QUT-Motorsport/QUTMS_Radio/RelatedImages/0150180559MolexFlatFlex.PNG

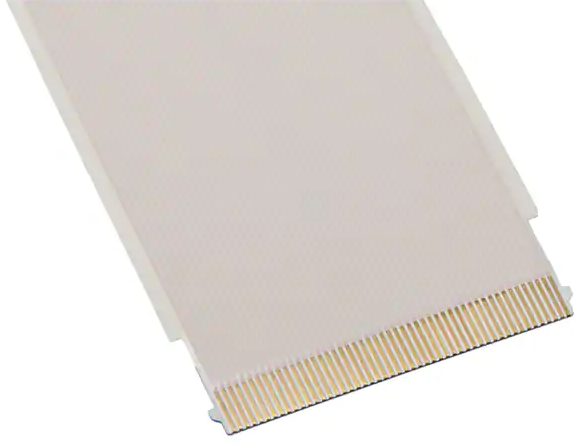
RelatedImages/0150180559MolexFlatFlex.PNG
