QUT-Motorsport/QUTMS_Radio/RelatedImages/bargraphDisplay.jpg

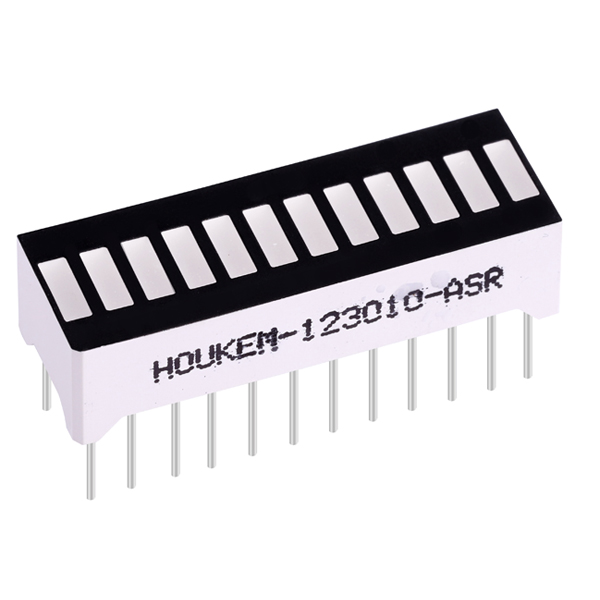
RelatedImages/bargraphDisplay.jpg
