QUT-Motorsport/QUTMS_Radio/RelatedImages/BMI-S-206-C.PNG

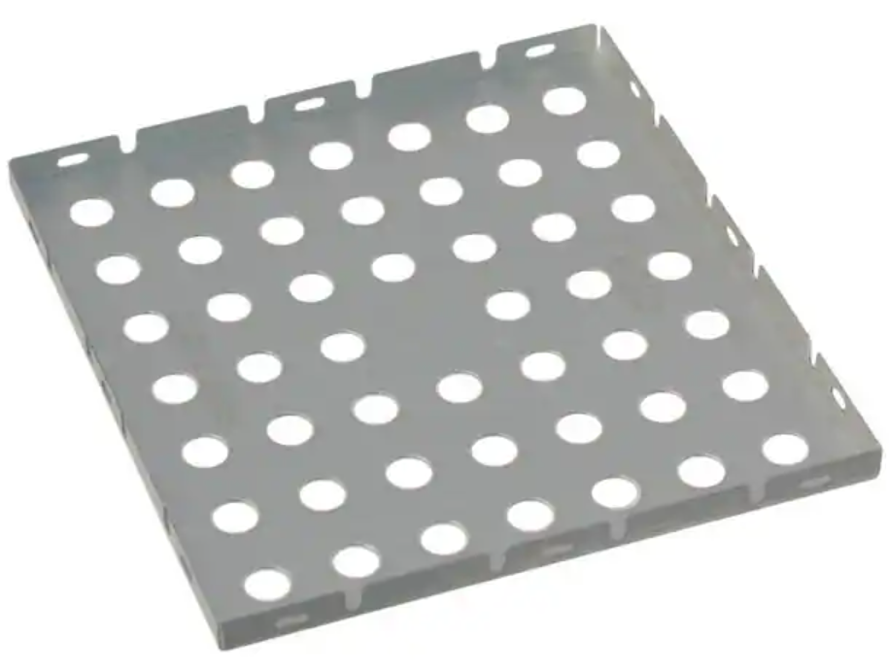
RelatedImages/BMI-S-206-C.PNG
