QUT-Motorsport/QUTMS_Radio/RelatedImages/BMI-S-206-F.PNG

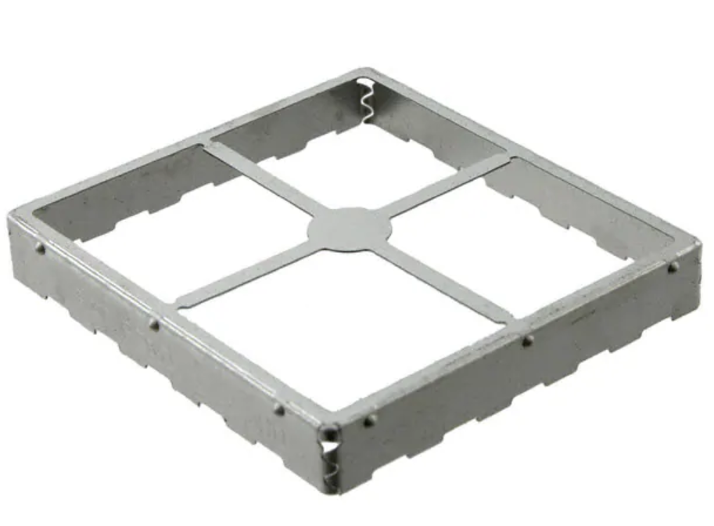
RelatedImages/BMI-S-206-F.PNG
