QUT-Motorsport/QUTMS_Radio/RelatedImages/cr2032battery.jpg

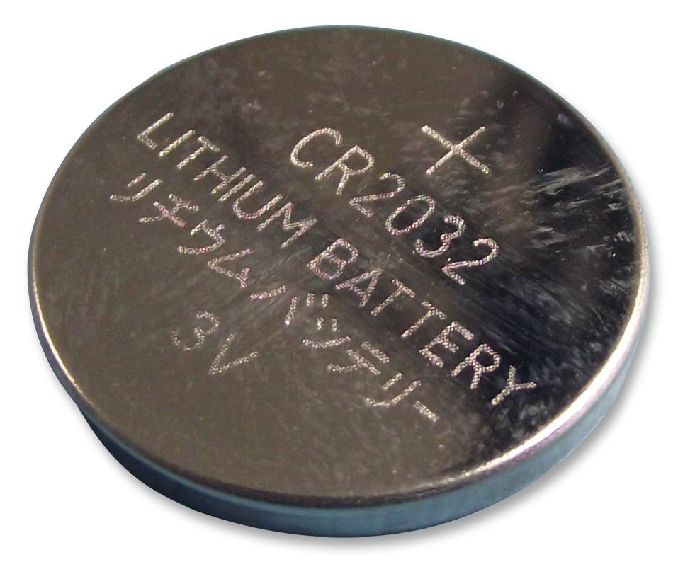
RelatedImages/cr2032battery.jpg
