QUT-Motorsport/QUTMS_Radio/RelatedImages/daughterBoardExample.png

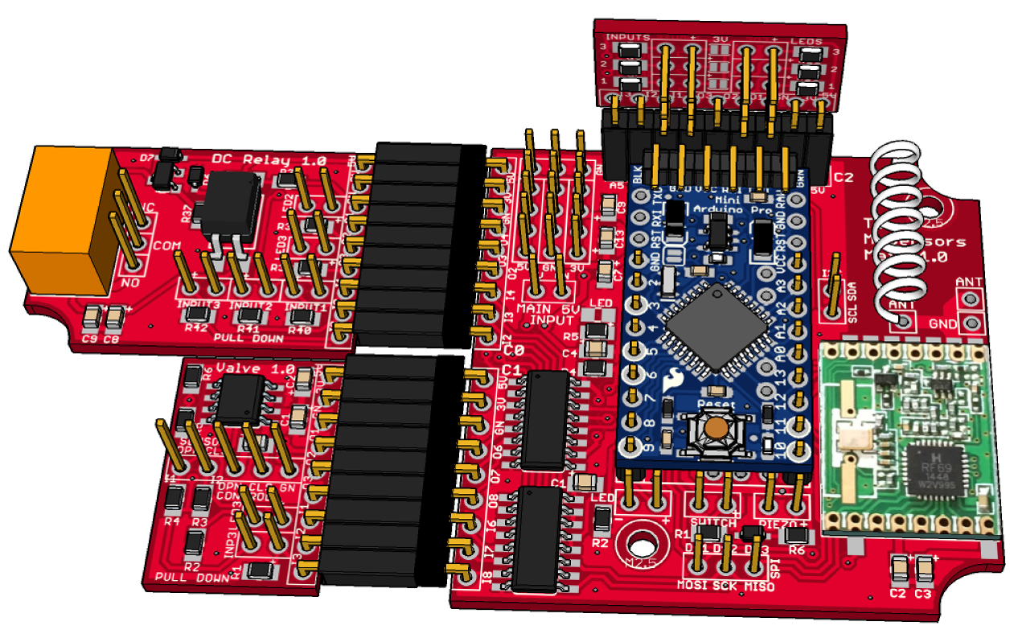
RelatedImages/daughterBoardExample.png
