QUT-Motorsport/QUTMS_Radio/RelatedImages/DBP868UA.PNG

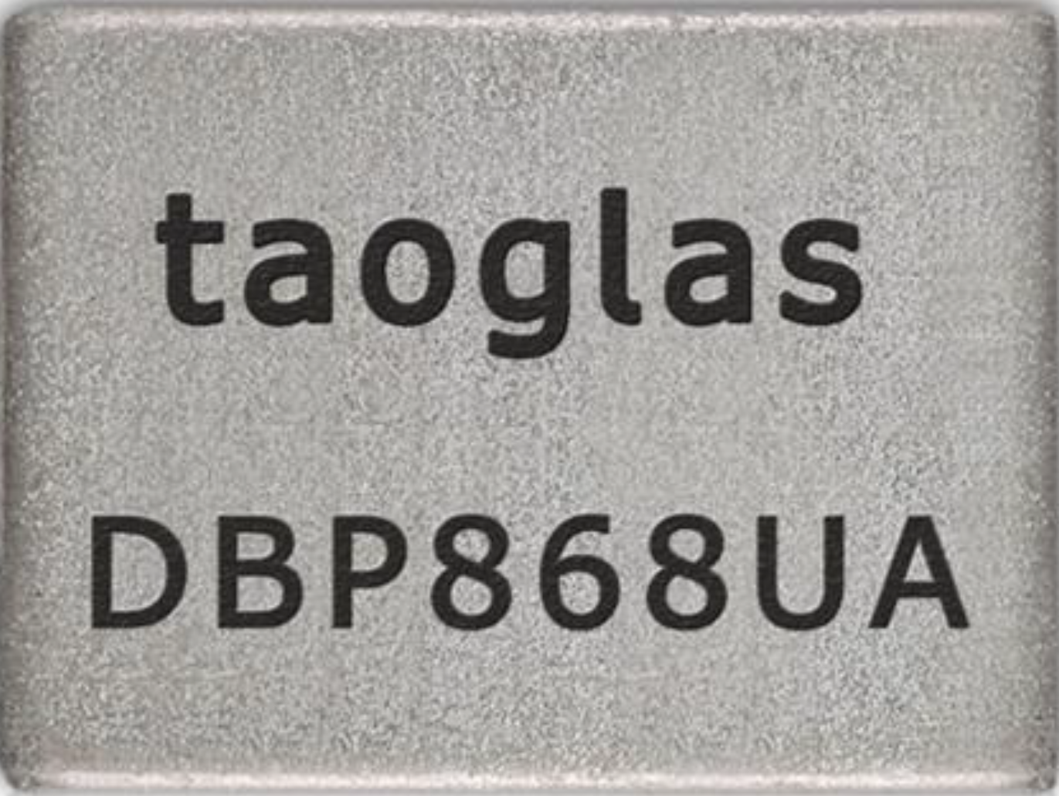
RelatedImages/DBP868UA.PNG
