QUT-Motorsport/QUTMS_Radio/RelatedImages/DBP915VA.PNG

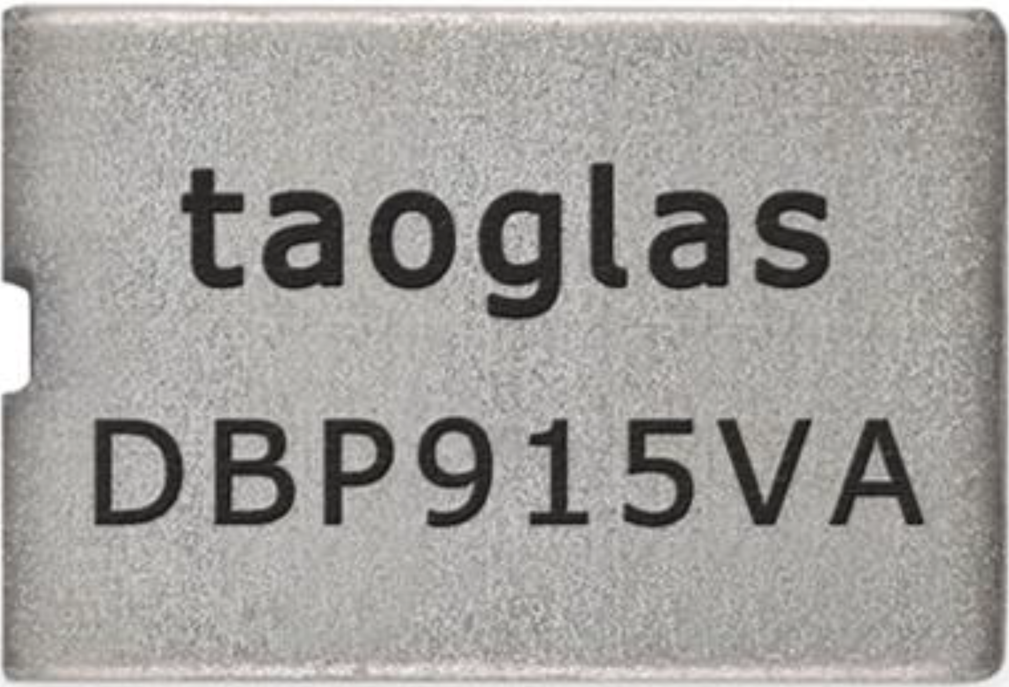
RelatedImages/DBP915VA.PNG
