QUT-Motorsport/QUTMS_Radio/RelatedImages/dcBarrelJack_PJ-102AH.PNG

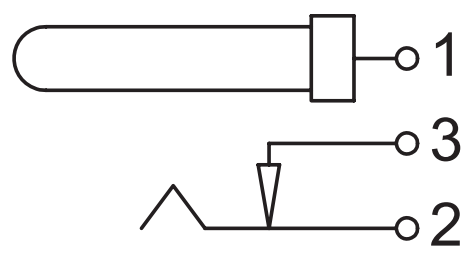
RelatedImages/dcBarrelJack_PJ-102AH.PNG
