QUT-Motorsport/QUTMS_Radio/RelatedImages/driverlessTrack.PNG

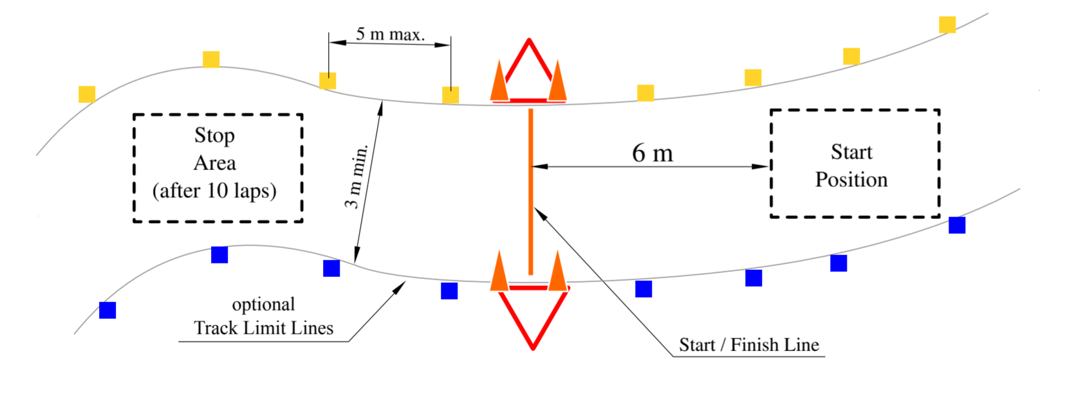
RelatedImages/driverlessTrack.PNG
