QUT-Motorsport/QUTMS_Radio/RelatedImages/dualMX120G.png

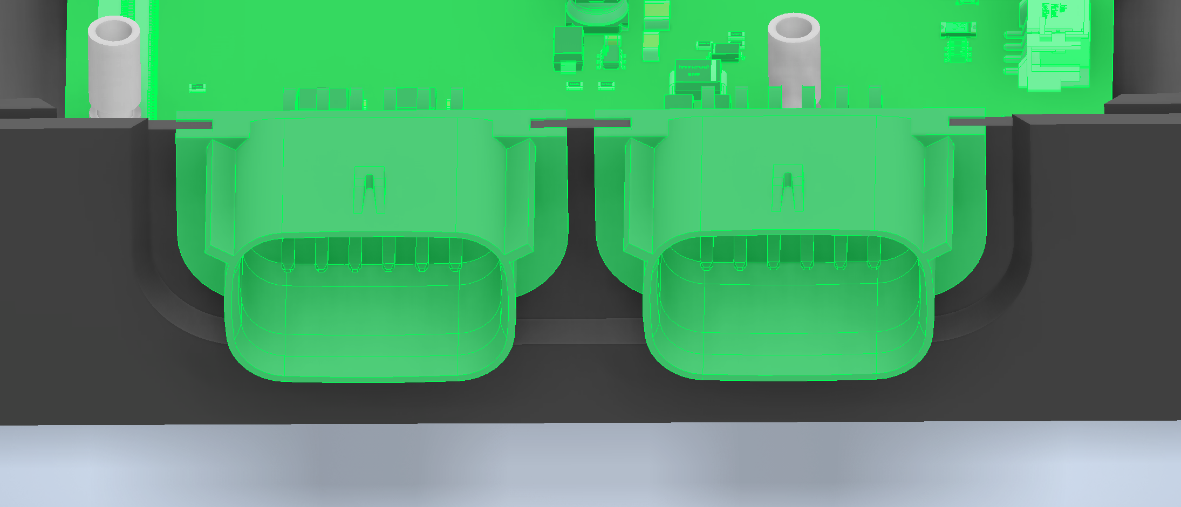
RelatedImages/dualMX120G.png
