QUT-Motorsport/QUTMS_Radio/RelatedImages/EOSRegions.png

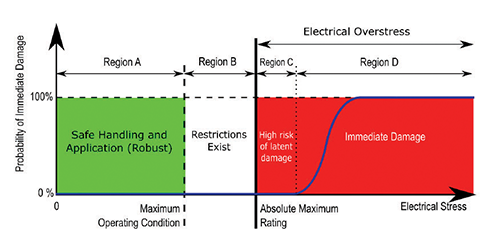
RelatedImages/EOSRegions.png
