QUT-Motorsport/QUTMS_Radio/RelatedImages/EOSRootCauses.png

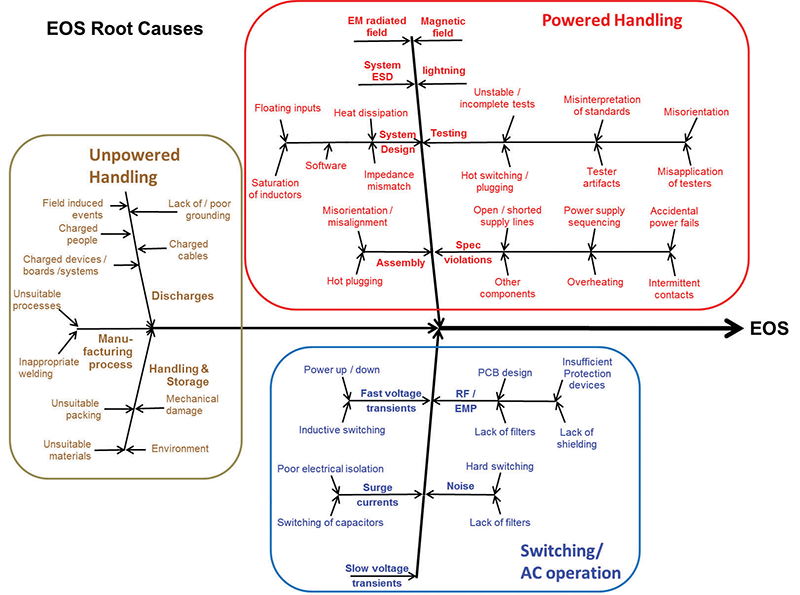
RelatedImages/EOSRootCauses.png
