QUT-Motorsport/QUTMS_Radio/RelatedImages/gnssComparisonGraph-01.png

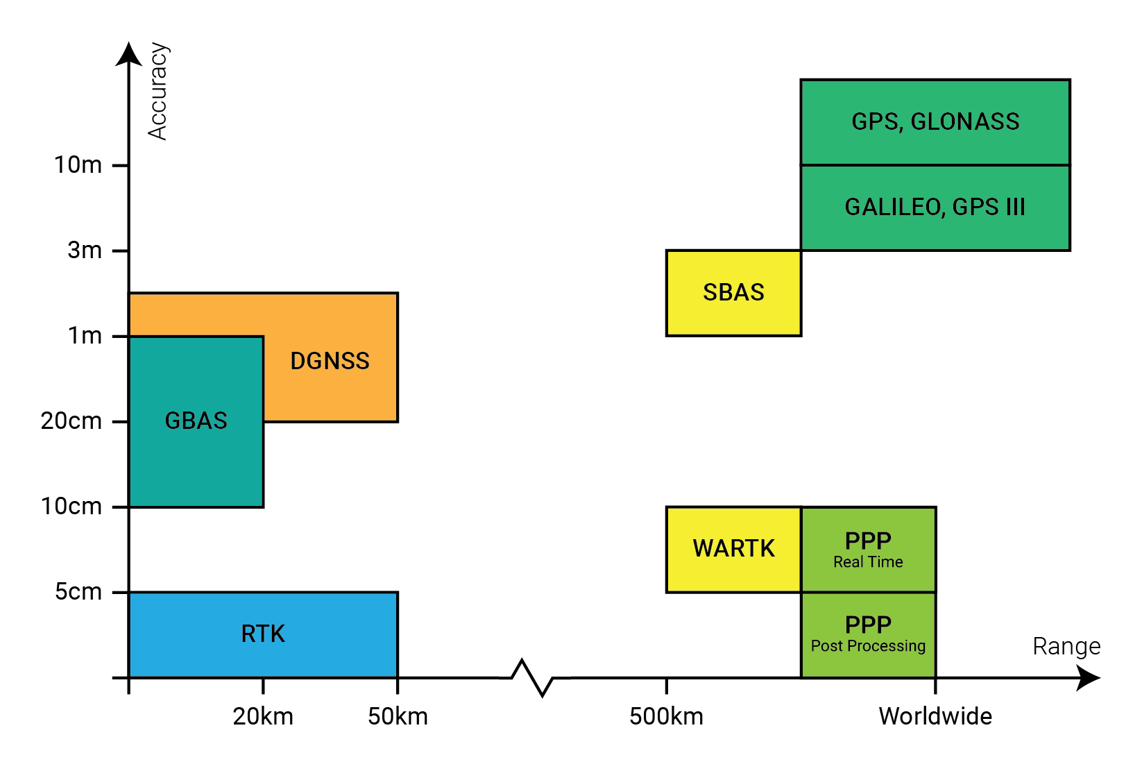
RelatedImages/gnssComparisonGraph-01.png
