QUT-Motorsport/QUTMS_Radio/RelatedImages/gpsSelection.PNG

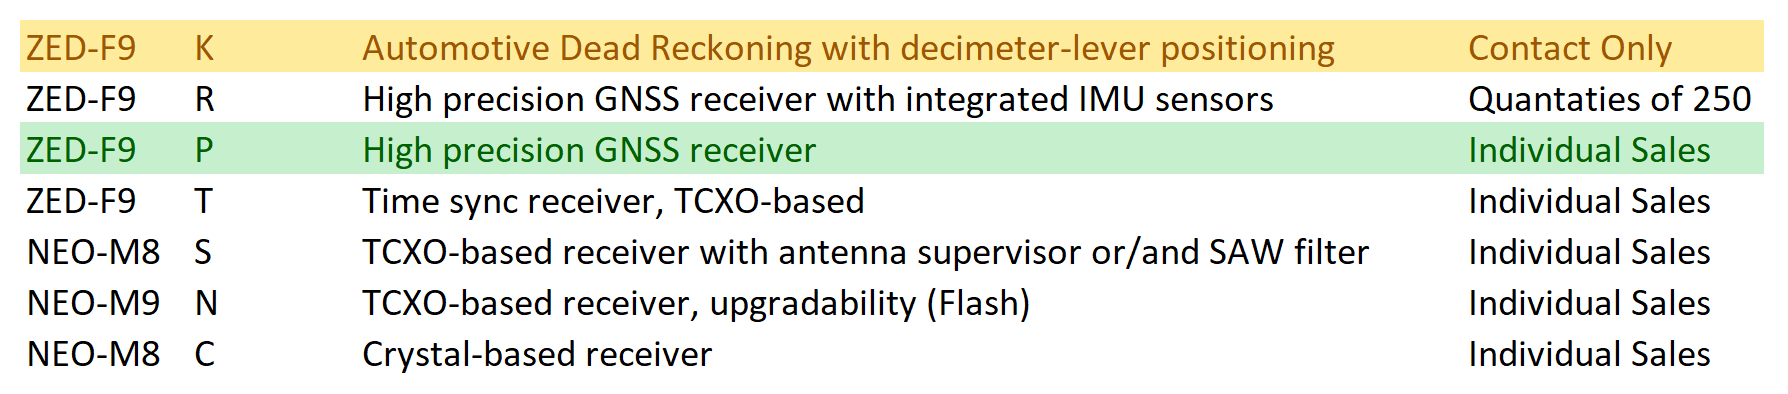
RelatedImages/gpsSelection.PNG
