QUT-Motorsport/QUTMS_Radio/RelatedImages/interimCaseTopDown.jpg

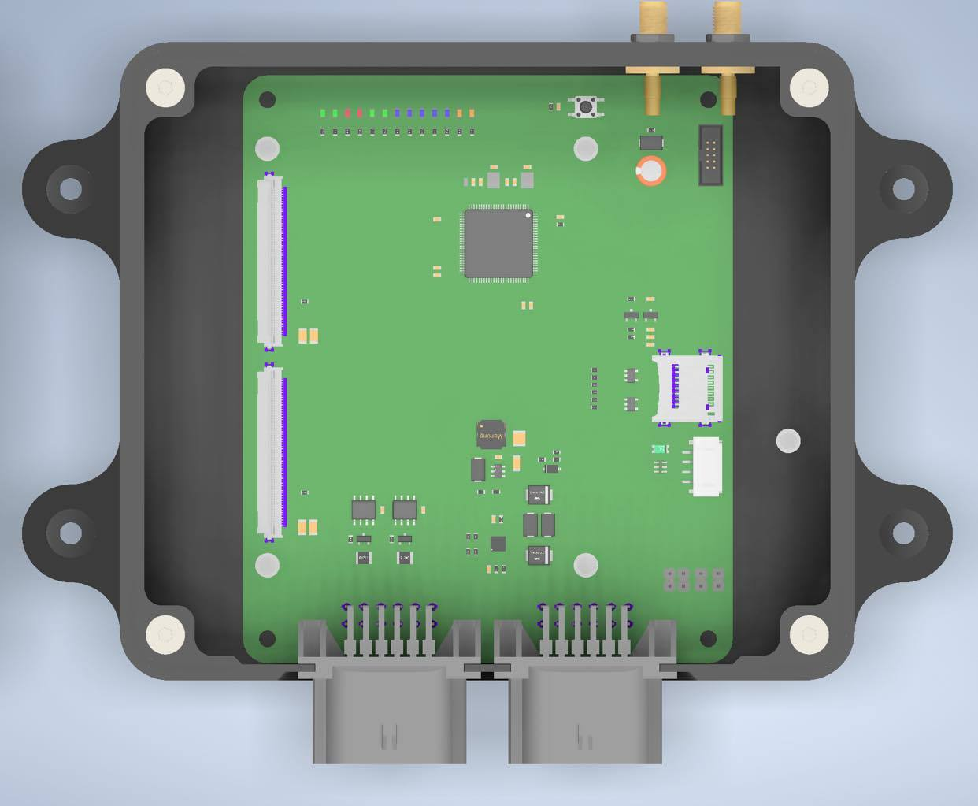
RelatedImages/interimCaseTopDown.jpg
