QUT-Motorsport/QUTMS_Radio/RelatedImages/m2mSelection.PNG

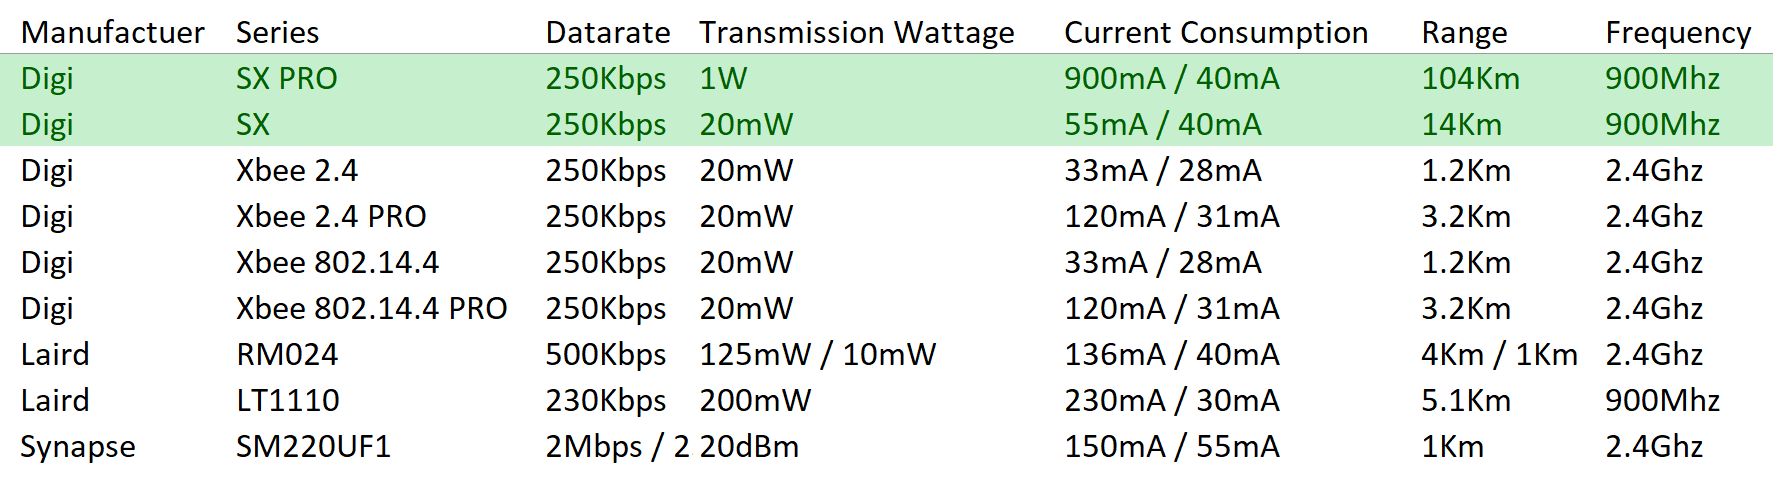
RelatedImages/m2mSelection.PNG
