QUT-Motorsport/QUTMS_Radio/RelatedImages/MX120G_FrontOn.PNG

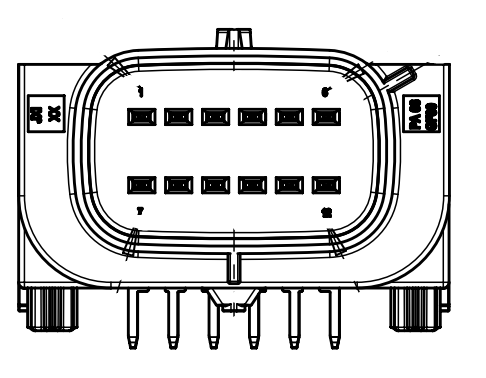
RelatedImages/MX120G_FrontOn.PNG
