QUT-Motorsport/QUTMS_Radio/RelatedImages/pcbWay4LayerStackUp.PNG

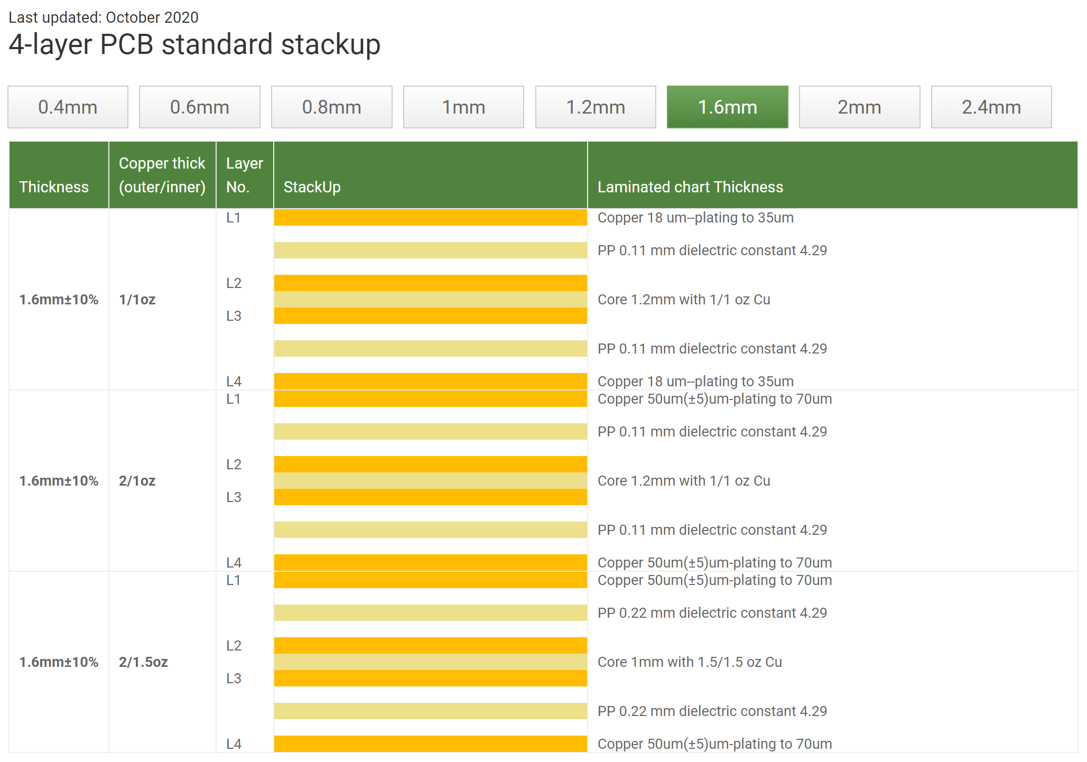
RelatedImages/pcbWay4LayerStackUp.PNG
