QUT-Motorsport/QUTMS_Radio/RelatedImages/RadioPodDistances-01.png

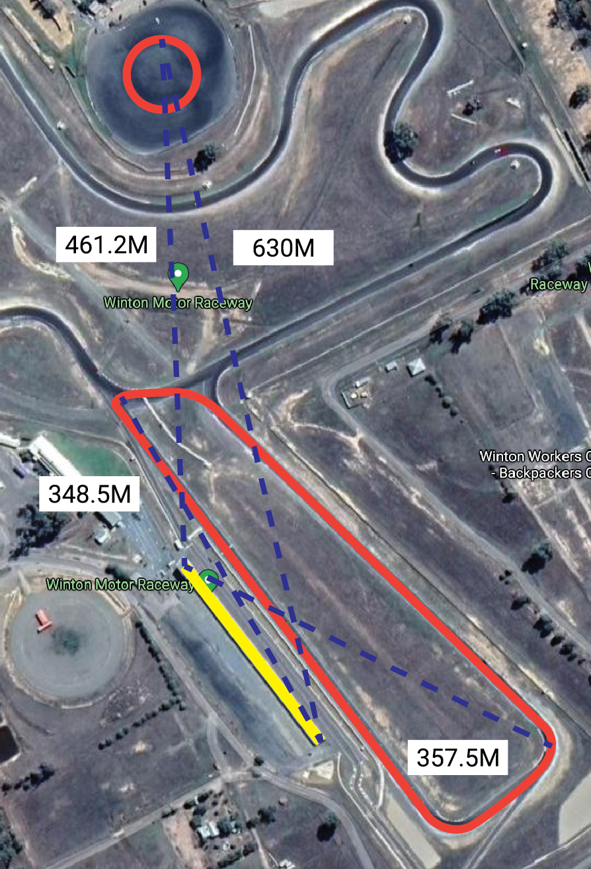
RelatedImages/RadioPodDistances-01.png
