QUT-Motorsport/QUTMS_Radio/RelatedImages/RadioPodDistances-02.png

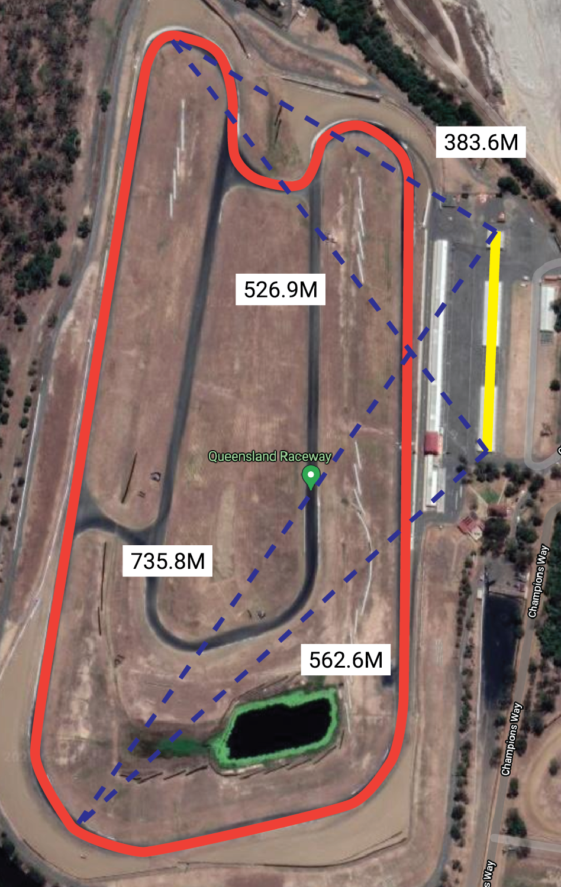
RelatedImages/RadioPodDistances-02.png
