QUT-Motorsport/QUTMS_Radio/RelatedImages/rtkImplimenation.PNG

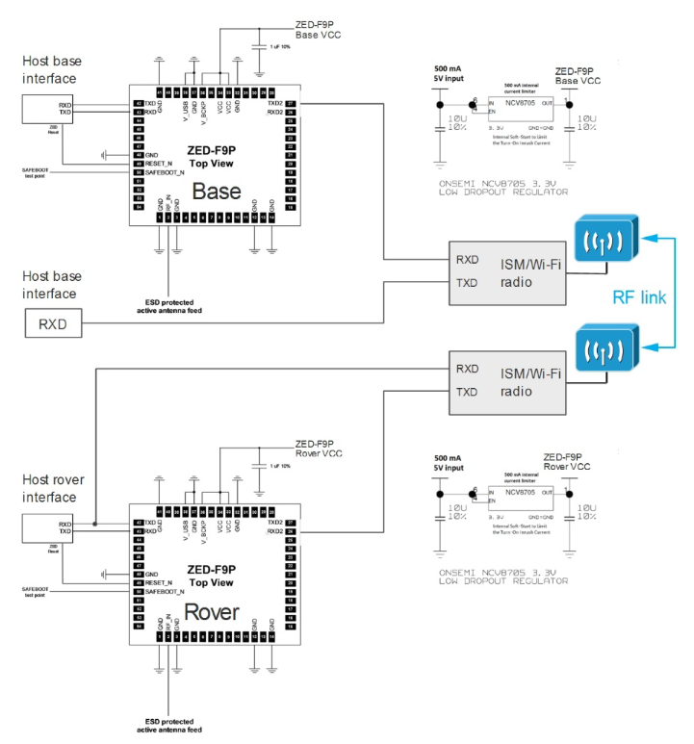
RelatedImages/rtkImplimenation.PNG
