QUT-Motorsport/QUTMS_Radio/RelatedImages/rulesFSGDriverlessRadioComms.PNG

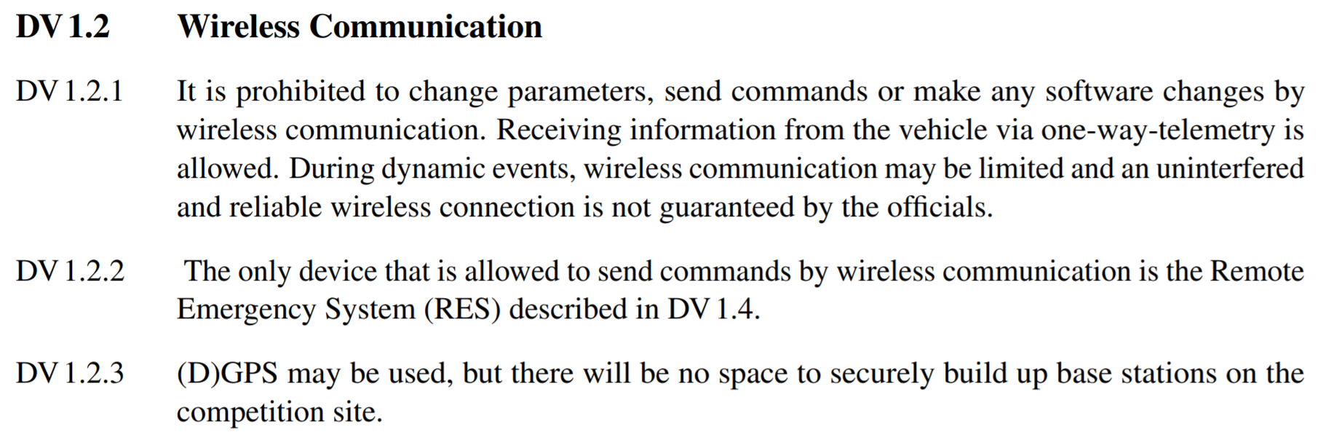
RelatedImages/rulesFSGDriverlessRadioComms.PNG
