QUT-Motorsport/QUTMS_Radio/RelatedImages/rulesFSGDriverlessSuppliedRadio.PNG

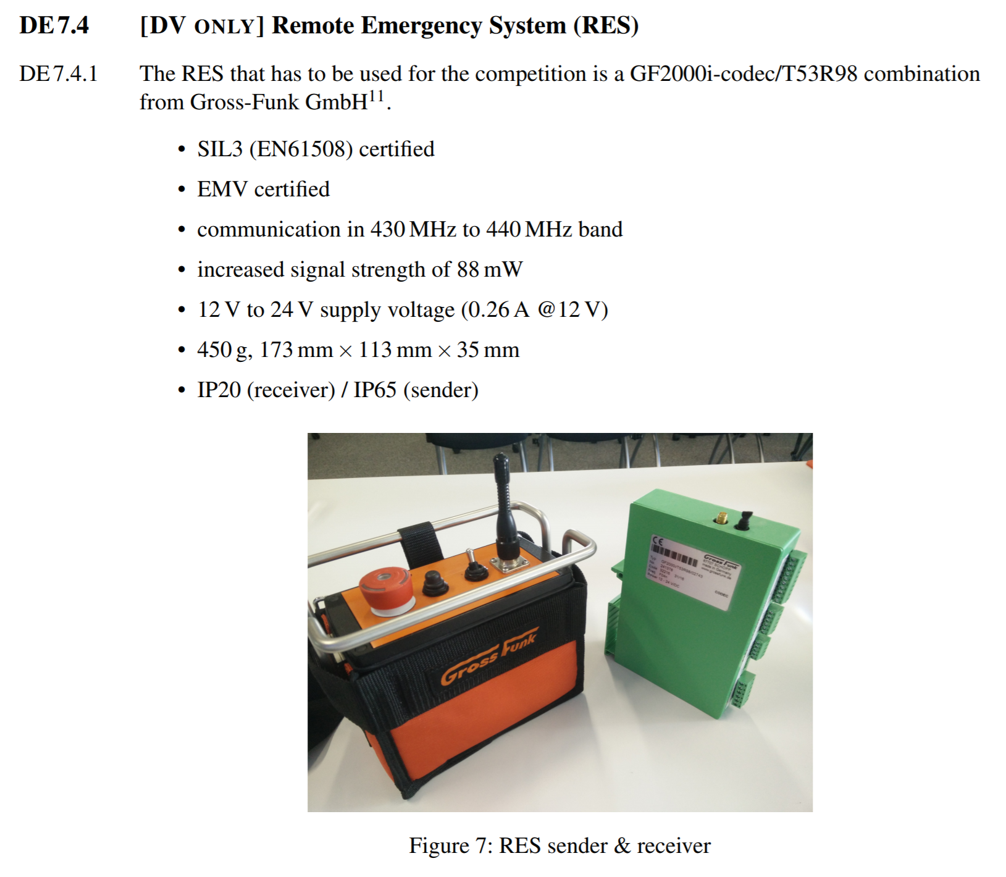
RelatedImages/rulesFSGDriverlessSuppliedRadio.PNG
