QUT-Motorsport/QUTMS_Radio/RelatedImages/serial_spi_i2c_yellow_1.5_inch_arduino_raspberry_pi_oled_display_128x64.jpg

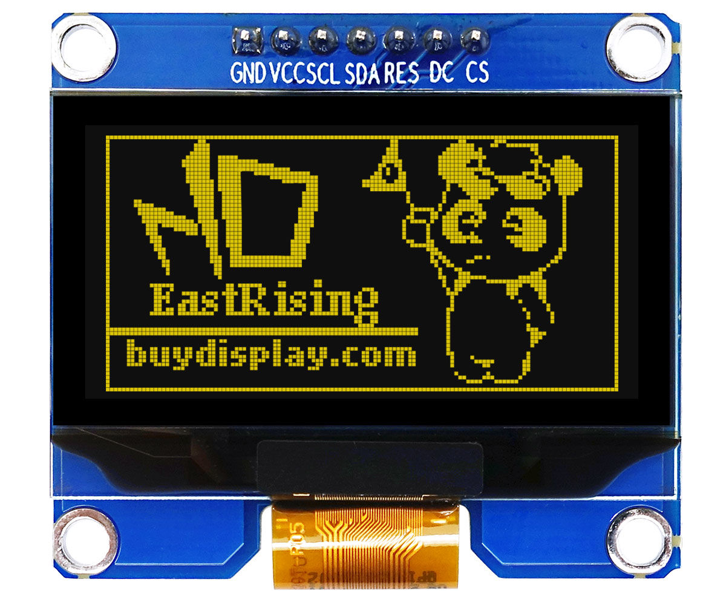
RelatedImages/serial_spi_i2c_yellow_1.5_inch_arduino_raspberry_pi_oled_display_128x64.jpg
