QUT-Motorsport/QUTMS_Radio/RelatedImages/sevenSegDisplay.png

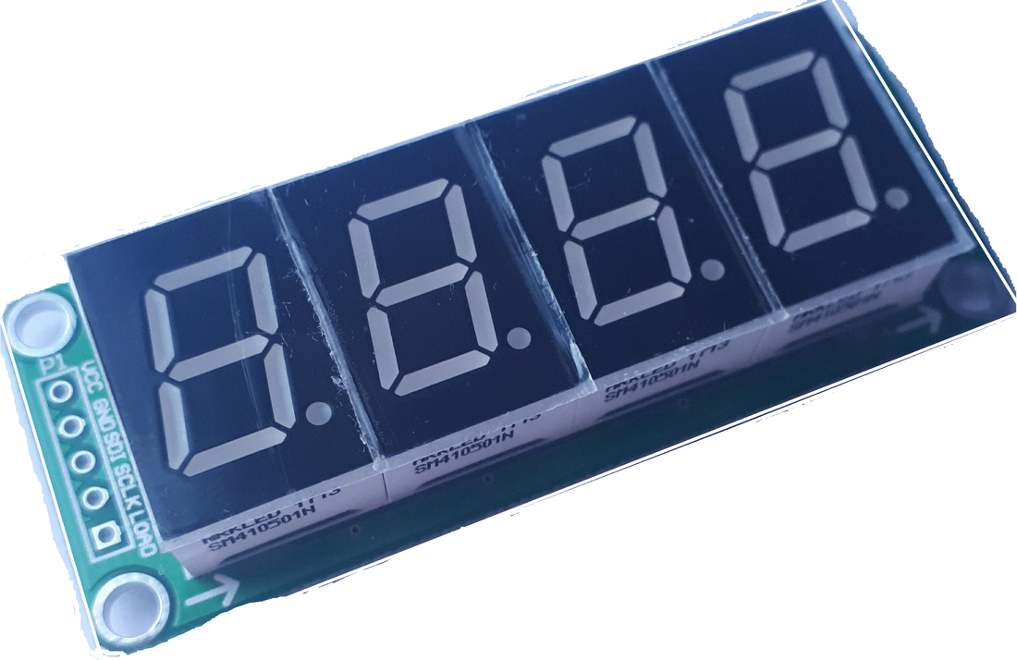
RelatedImages/sevenSegDisplay.png
