QUT-Motorsport/QUTMS_Radio/RelatedImages/supercapGenericImage.PNG

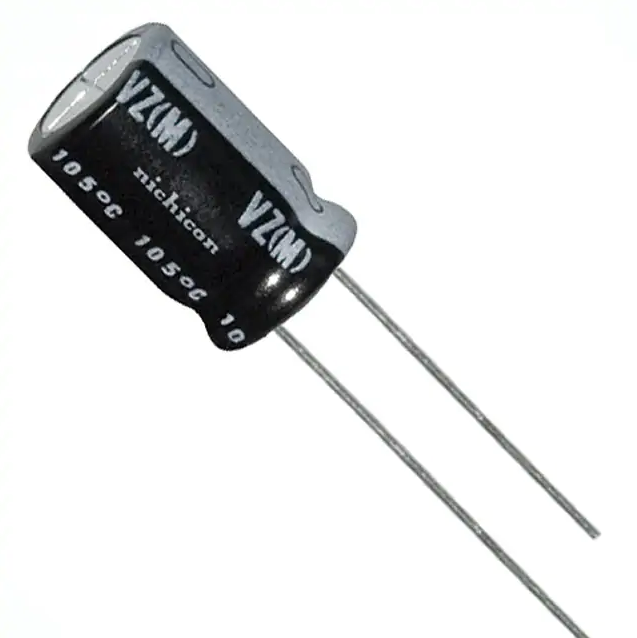
RelatedImages/supercapGenericImage.PNG
