QUT-Motorsport/QUTMS_Radio/RelatedImages/taoglasAntenna_AA200151111.PNG

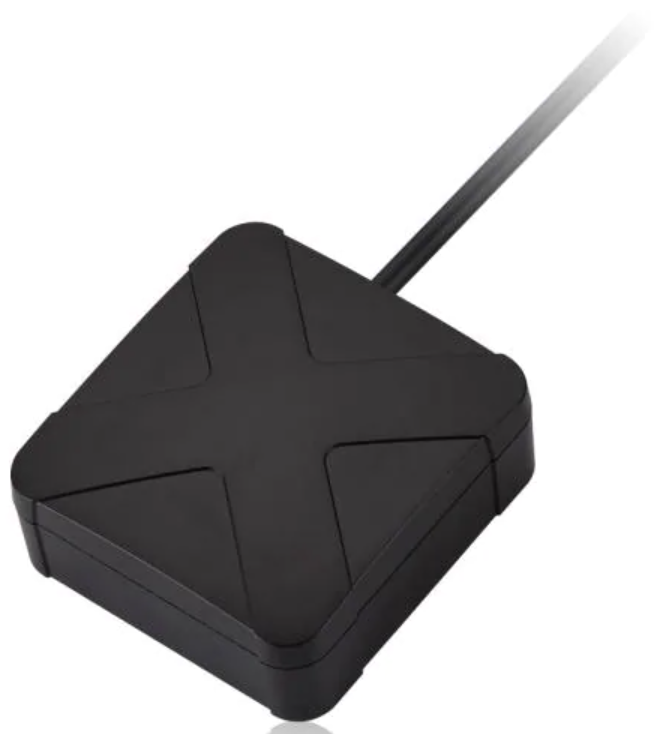
RelatedImages/taoglasAntenna_AA200151111.PNG
