QUT-Motorsport/QUTMS_Radio/RelatedImages/taoglasAntennaISM.PNG

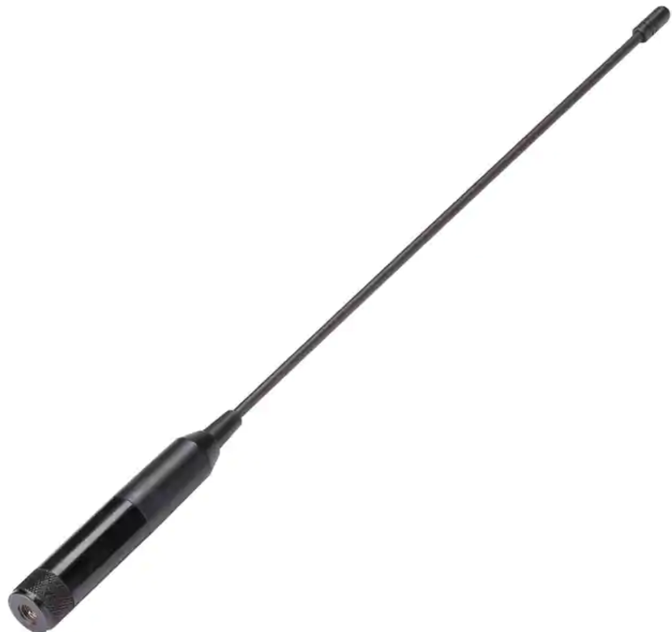
RelatedImages/taoglasAntennaISM.PNG
