QUT-Motorsport/QUTMS_Radio/RelatedImages/u-blox ZED-F9P decal.png

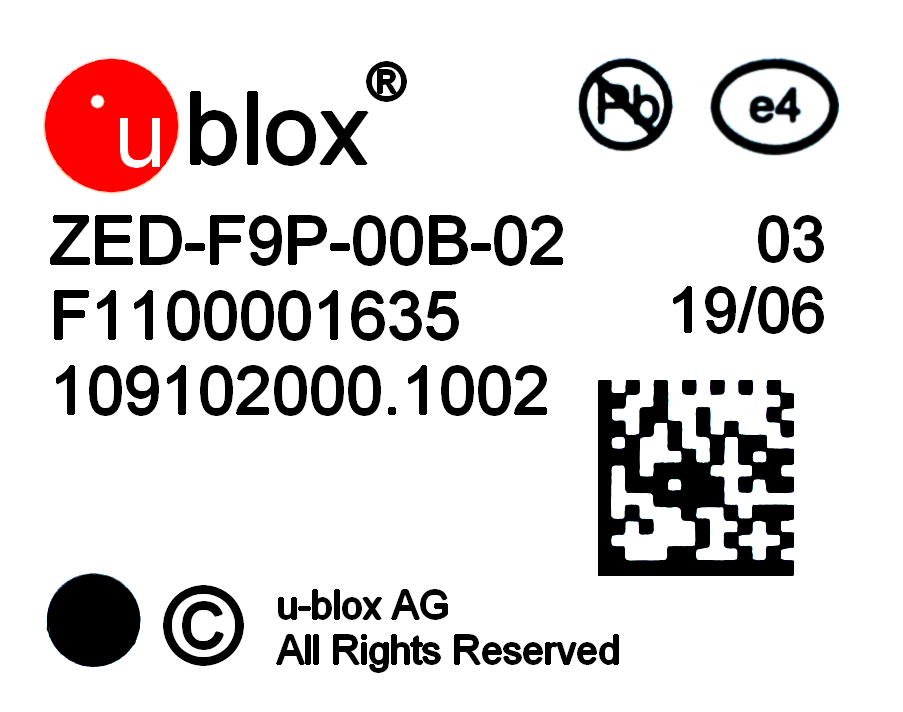
RelatedImages/u-blox ZED-F9P decal.png
