QUT-Motorsport/QUTMS_Radio/RelatedImages/ublox_FullColor_CMYK_pos_0.jpg

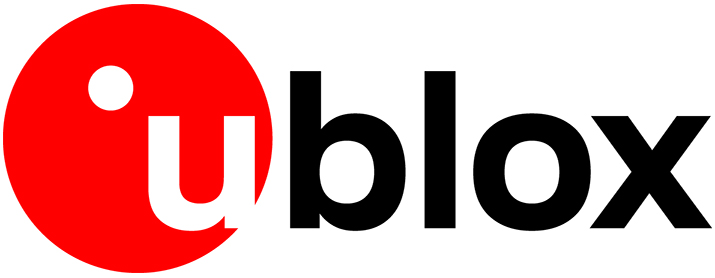
RelatedImages/ublox_FullColor_CMYK_pos_0.jpg
