QUT-Motorsport/QUTMS_Radio/3DModels/OLEDDisplay1-3inch.stp

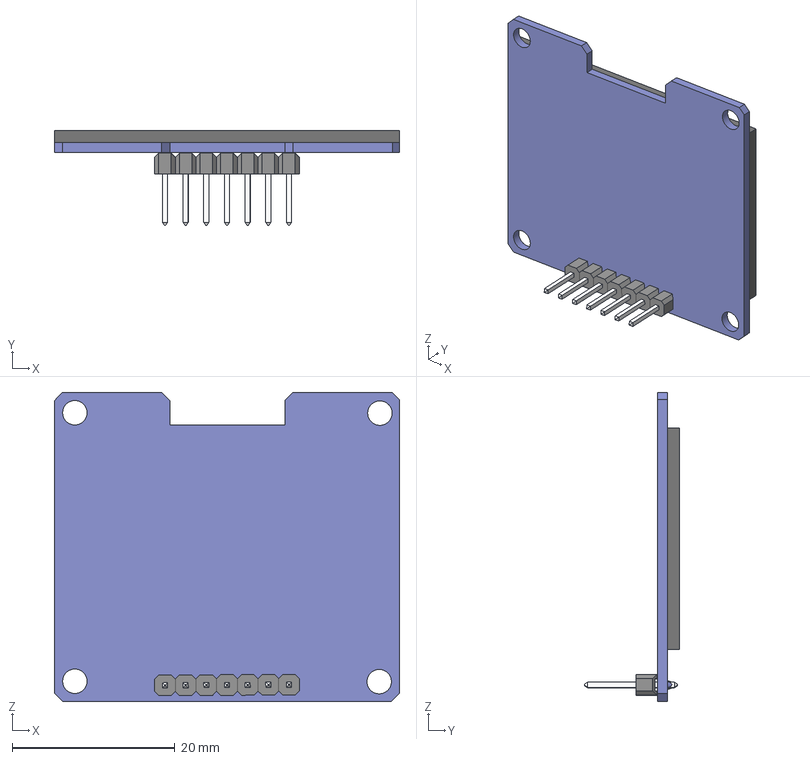
[picture p52: CAD file, 2021-02-18]
3DModels/OLEDDisplay1-3inch.stp
42.4 x 11.7 x 38.0 mm
