QUT-Motorsport/QUTMS_Radio/3DModels/1812_RES.stp

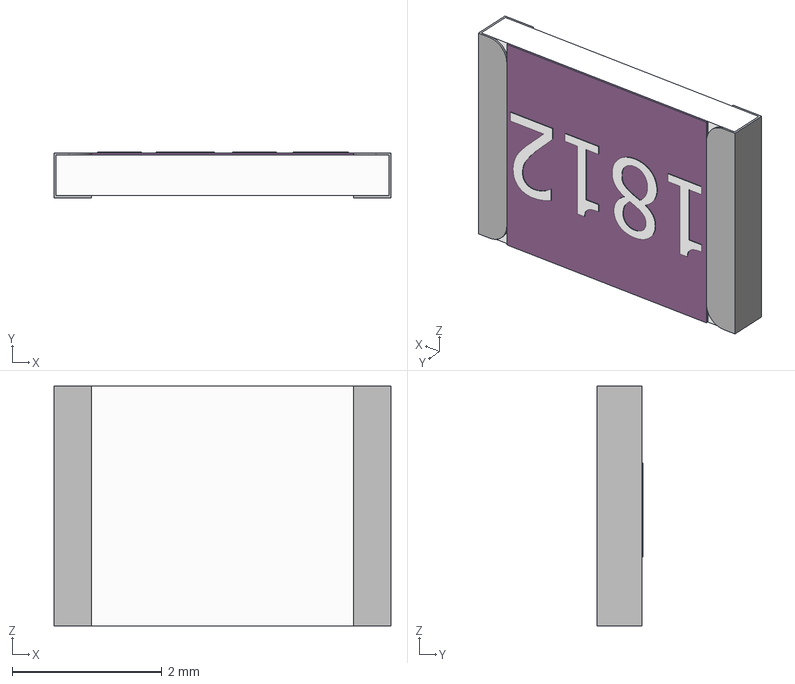
[picture p53: CAD file, 2021-02-15]
3DModels/1812_RES.stp
4.50 x 0.61 x 3.20 mm
Capsule
Encapsulation x 2
TopCover
