QUT-Motorsport/QUTMS_Radio/3DModels/TSSOP-14 0.65p 4.4mm.step

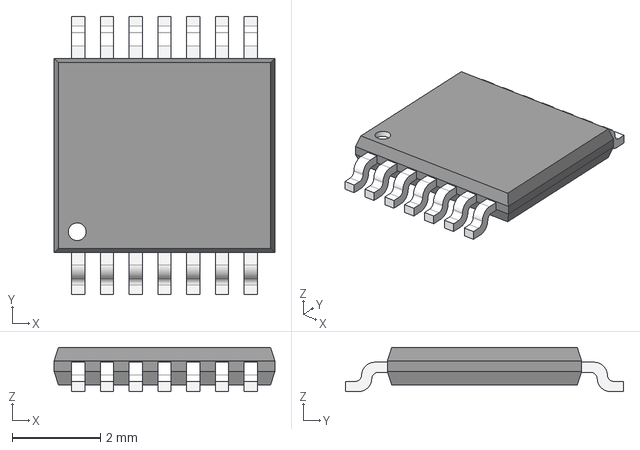
[picture p54: CAD file, 2021-02-15]
3DModels/TSSOP-14 0.65p 4.4mm.step
5.00 x 6.30 x 1.00 mm
