QUT-Motorsport/QUTMS_Radio/3DModels/pqfpfp144_p0-5_l20_w20.stp

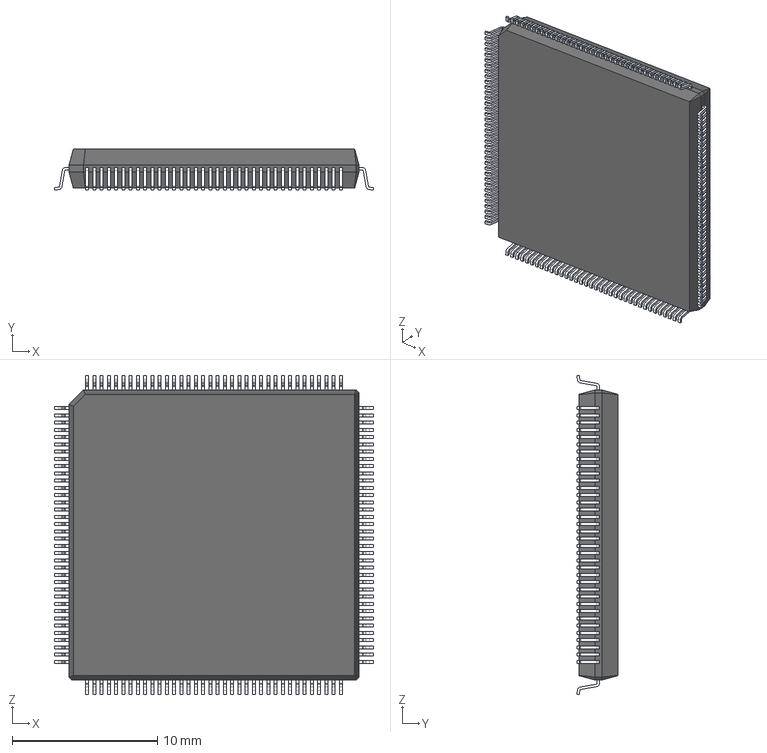
[picture p55: CAD file, 2021-02-11]
3DModels/pqfpfp144_p0-5_l20_w20.stp
22.0 x 2.83 x 22.0 mm
