QUT-Motorsport/QUTMS_Radio/3DModels/hexagonal_spacer_MF_M3_H10_HEX5_FTD6_MTL8.step

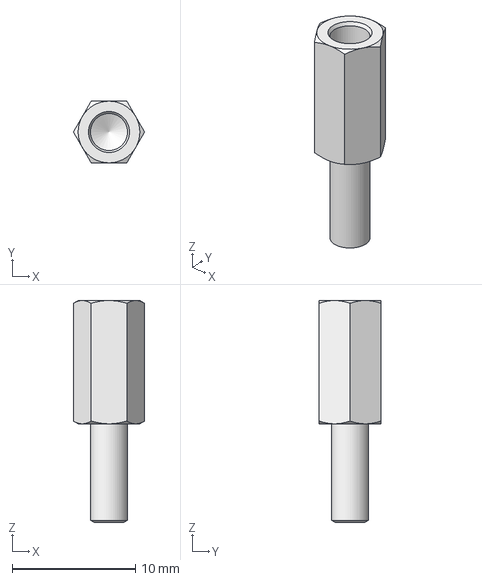
[picture p57: CAD file, 2021-02-09]
3DModels/hexagonal_spacer_MF_M3_H10_HEX5_FTD6_MTL8.step
5.78 x 5.01 x 18.0 mm
