QUT-Motorsport/QUTMS_Radio/3DModels/hexagonal_spacer_MF_M3_H08_HEX5_FTD4_MTL8.step

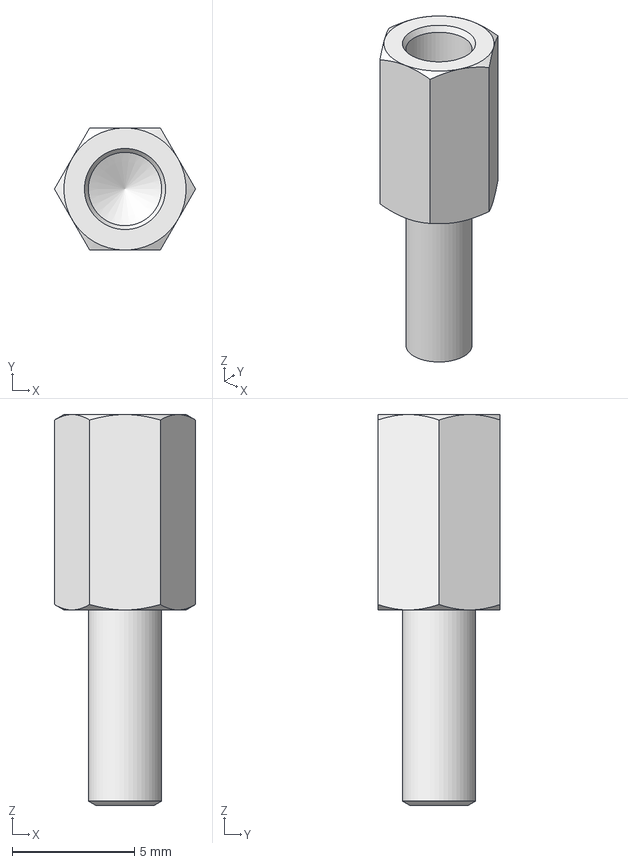
[picture p58: CAD file, 2021-02-09]
3DModels/hexagonal_spacer_MF_M3_H08_HEX5_FTD4_MTL8.step
5.78 x 5.01 x 16.0 mm
