QUT-Motorsport/QUTMS_Radio/3DModels/hexagonal_spacer_MF_M3_H12_HEX5_FTD8_MTL8.step

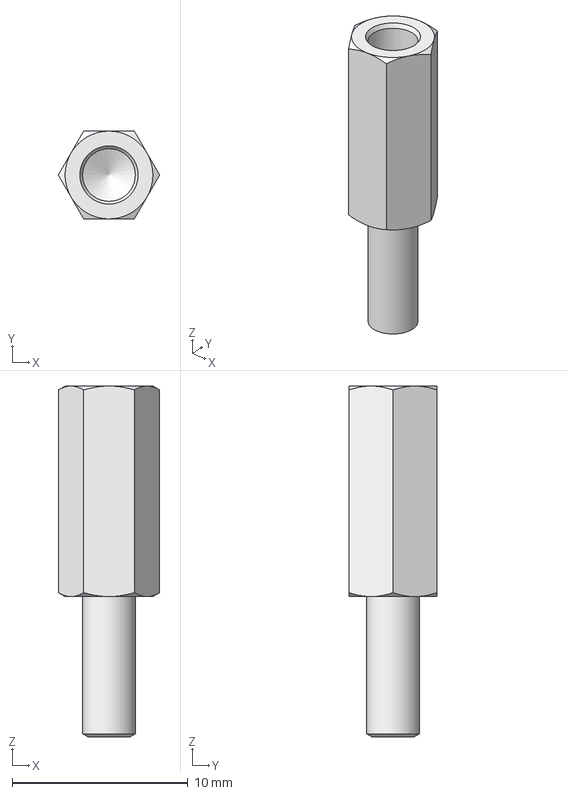
[picture p59: CAD file, 2021-02-09]
3DModels/hexagonal_spacer_MF_M3_H12_HEX5_FTD8_MTL8.step
5.78 x 5.01 x 20.0 mm
