QUT-Motorsport/QUTMS_Radio/3DModels/TSW-104-08-T-D-RA.stp

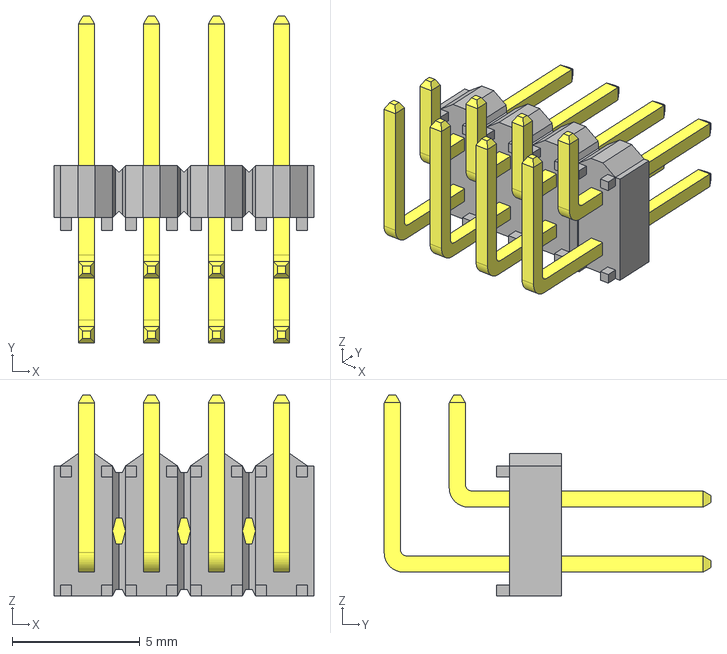
[picture p60: CAD file, 2021-02-08]
3DModels/TSW-104-08-T-D-RA.stp
10.2 x 12.8 x 7.85 mm
_TSW-104-08-T-D-RA_body
_T-1S6-08-TSW-1-08-4-RA-D
