QUT-Motorsport/QUTMS_Radio/3DModels/20-Pin Shrouded Header (IDC) Straight.stp

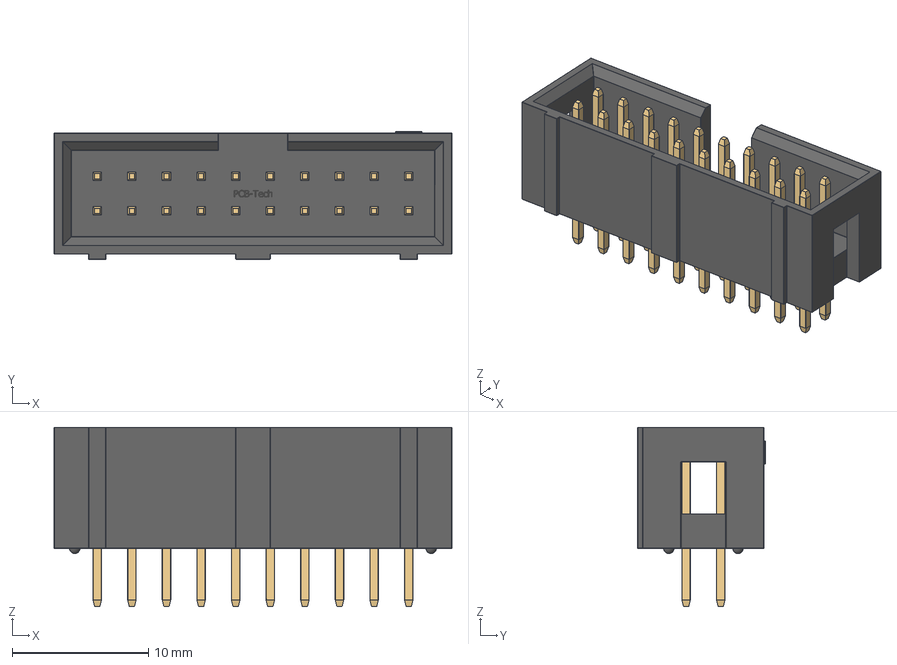
[picture p61: CAD file, 2021-02-08]
3DModels/20-Pin Shrouded Header (IDC) Straight.stp
29.2 x 9.37 x 13.2 mm
Straight Contact x 20
20-Pin Shrouded Header Body
