QUT-Motorsport/QUTMS_Radio/3DModels/LQFP100_14X14X1.6_P0.5_ST.step

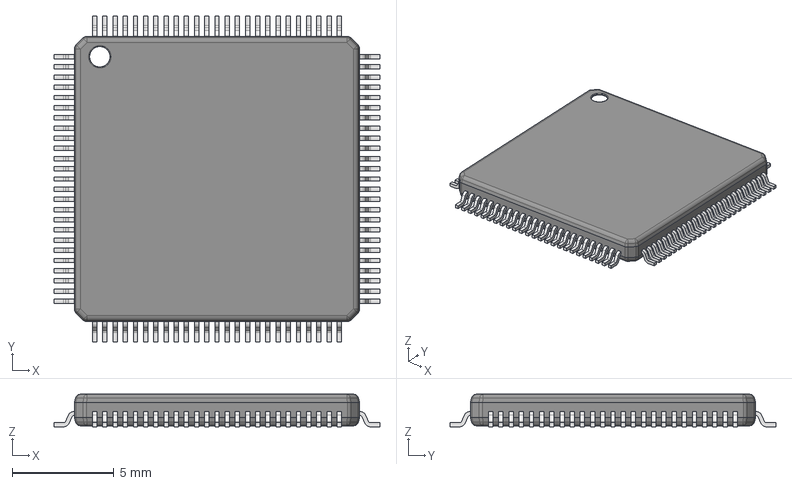
[picture p62: CAD file, 2021-02-05]
3DModels/LQFP100_14X14X1.6_P0.5_ST.step
16.0 x 16.0 x 1.60 mm
