QUT-Motorsport/QUTMS_Radio/3DModels/Aluminum_electrolytic_capacitor_radial_D6.3_H9_PinD0.5_Pitch2.5_nominal_orange.step

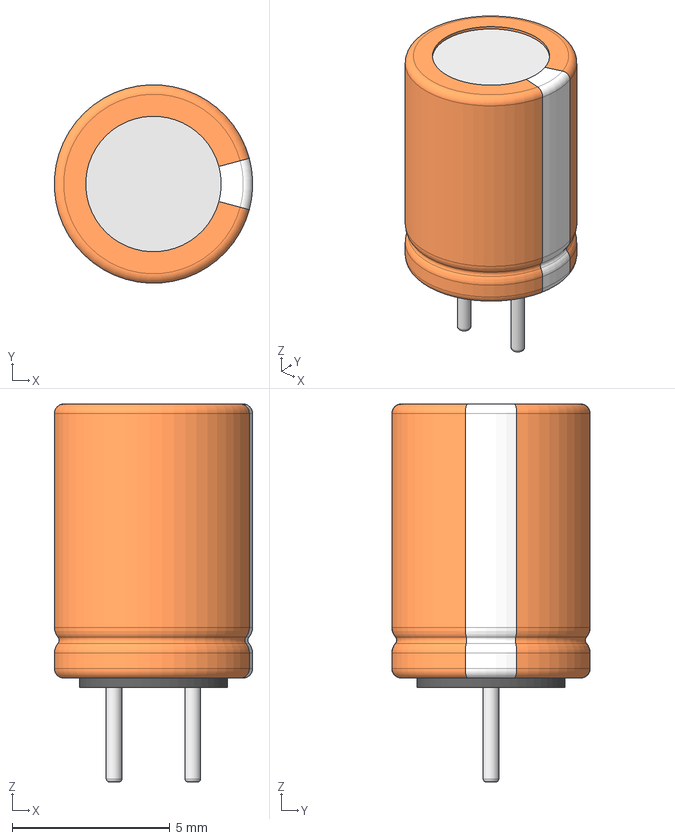
[picture p63: CAD file, 2021-02-04]
3DModels/Aluminum_electrolytic_capacitor_radial_D6.3_H9_PinD0.5_Pitch2.5_nominal_orange.step
6.29 x 6.30 x 12.0 mm
