QUT-Motorsport/QUTMS_Radio/3DModels/JST - PH - SMD (R) - 4Pin - 2.00mm.stp

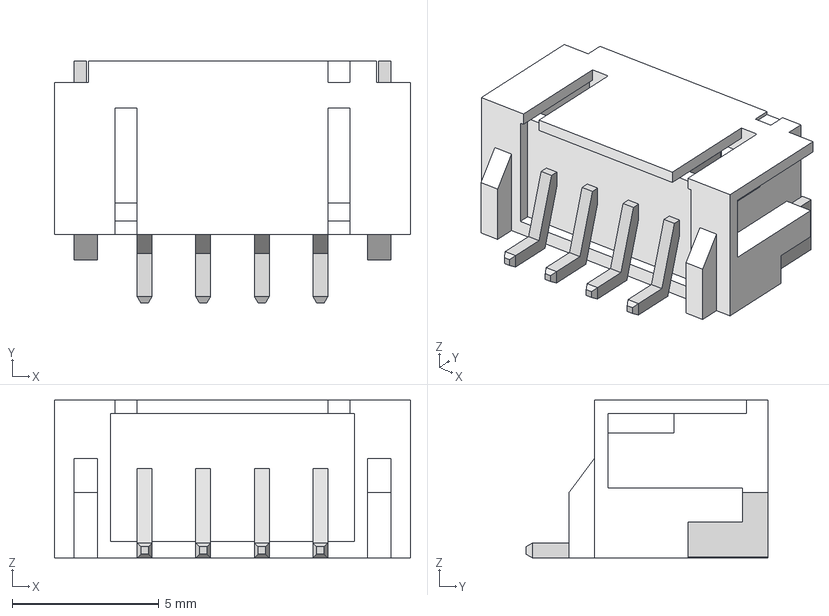
[picture p64: CAD file, 2021-02-04]
3DModels/JST - PH - SMD (R) - 4Pin - 2.00mm.stp
12.1 x 8.26 x 5.38 mm
