QUT-Motorsport/QUTMS_Radio/3DModels/JST - PH - Thru (V) - 4Pin - 2.00mm.stp

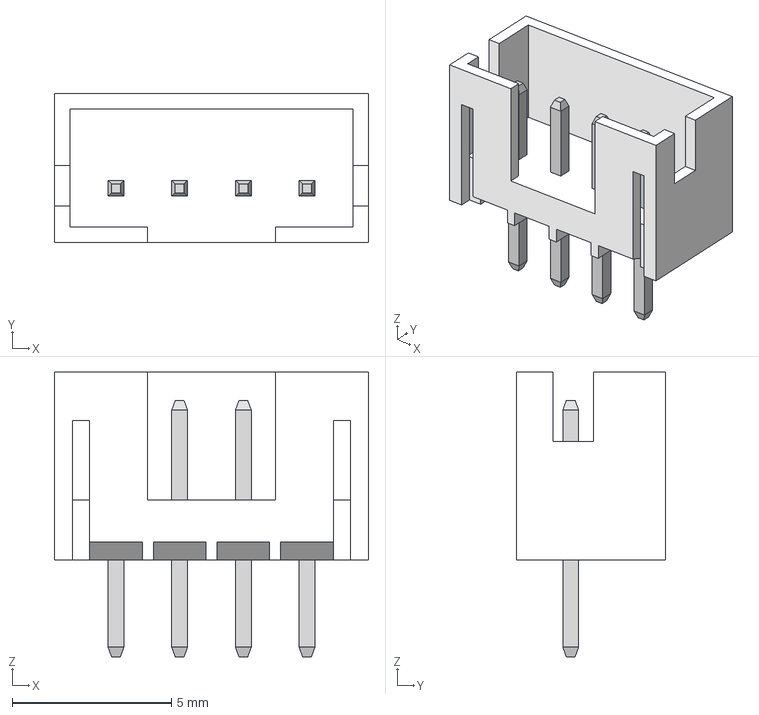
[picture p65: CAD file, 2021-02-04]
3DModels/JST - PH - Thru (V) - 4Pin - 2.00mm.stp
9.86 x 4.67 x 8.94 mm
