QUT-Motorsport/QUTMS_Radio/3DModels/SOT-223-6.step

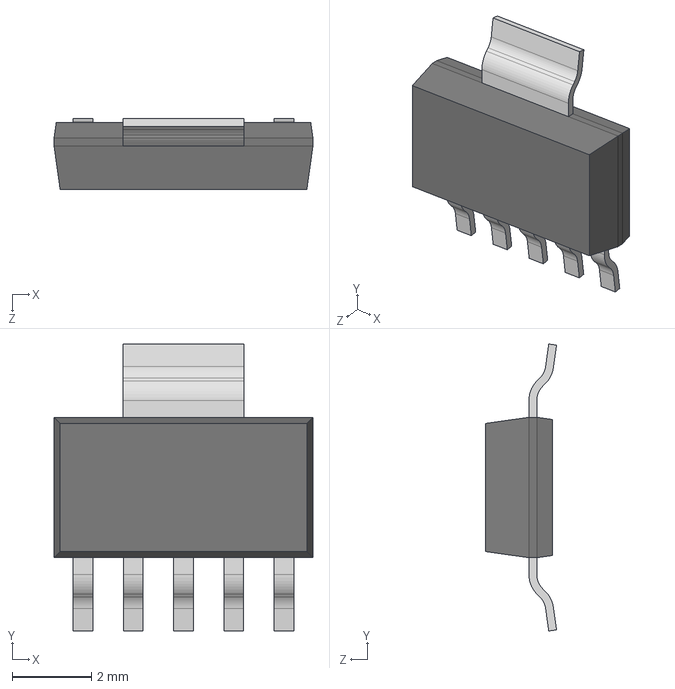
[picture p66: CAD file, 2021-02-04]
3DModels/SOT-223-6.step
6.55 x 7.26 x 1.80 mm
