QUT-Motorsport/QUTMS_Radio/3DModels/keystone-PN2898.STEP

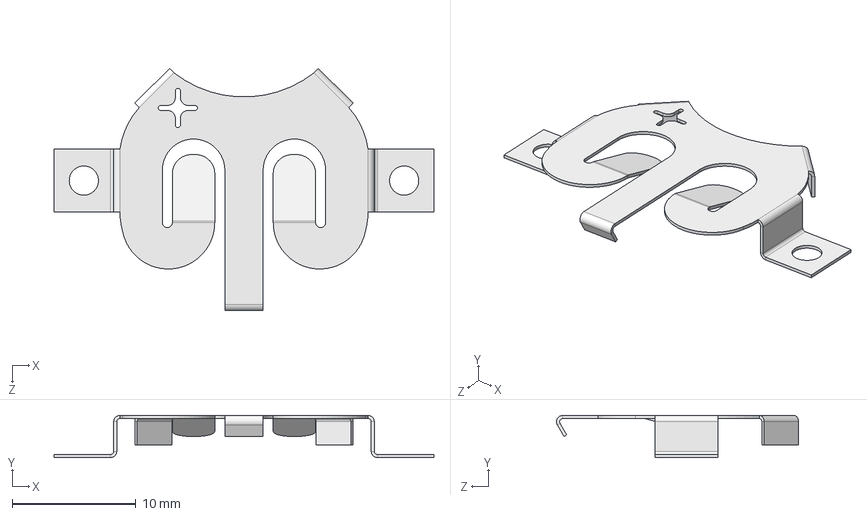
[picture p67: CAD file, 2021-02-03]
3DModels/keystone-PN2898.STEP
30.7 x 3.40 x 19.6 mm
