QUT-Motorsport/QUTMS_Radio/3DModels/U.FL-R-SMT(10)--3DModel-STEP-56544.STEP

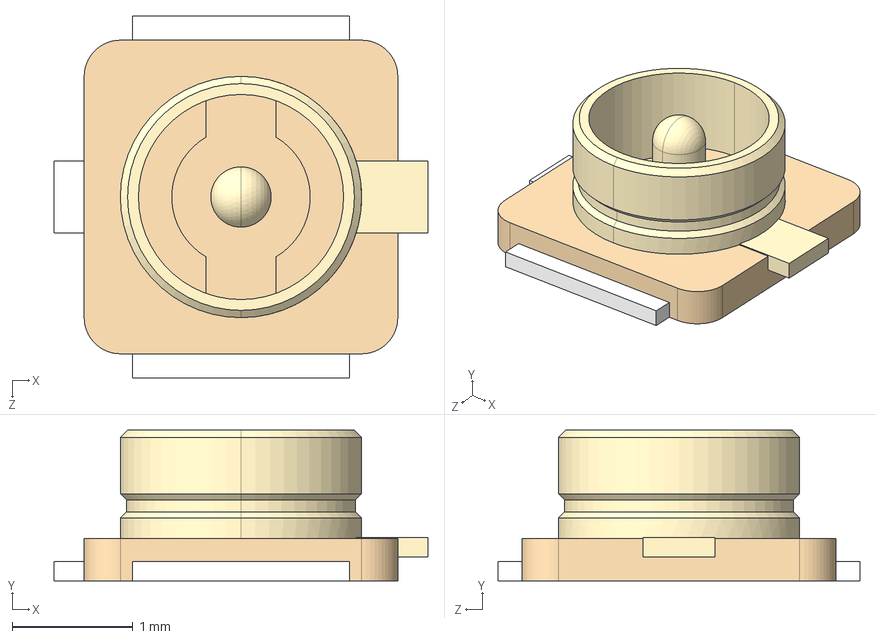
[picture p68: CAD file, 2021-02-03]
3DModels/U.FL-R-SMT(10)--3DModel-STEP-56544.STEP
3.10 x 1.25 x 3.00 mm
