QUT-Motorsport/QUTMS_Radio/3DModels/NFE31PT101C1E9L.STEP

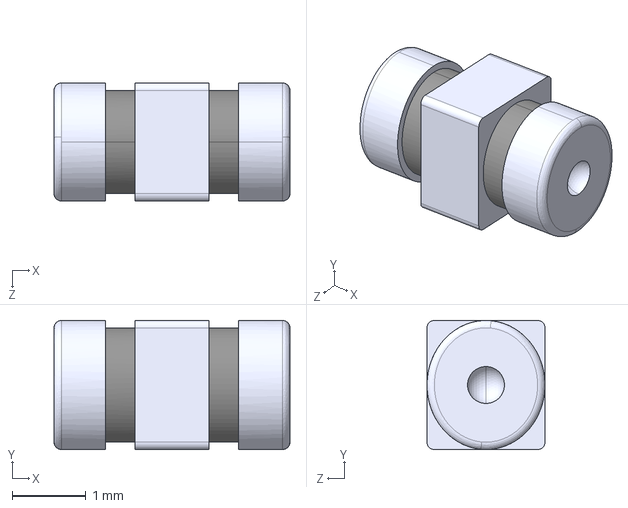
[picture p69: CAD file, 2021-02-02]
3DModels/NFE31PT101C1E9L.STEP
3.20 x 1.75 x 1.60 mm
