QUT-Motorsport/QUTMS_Radio/3DModels/c-1734517-1-b-3d.stp

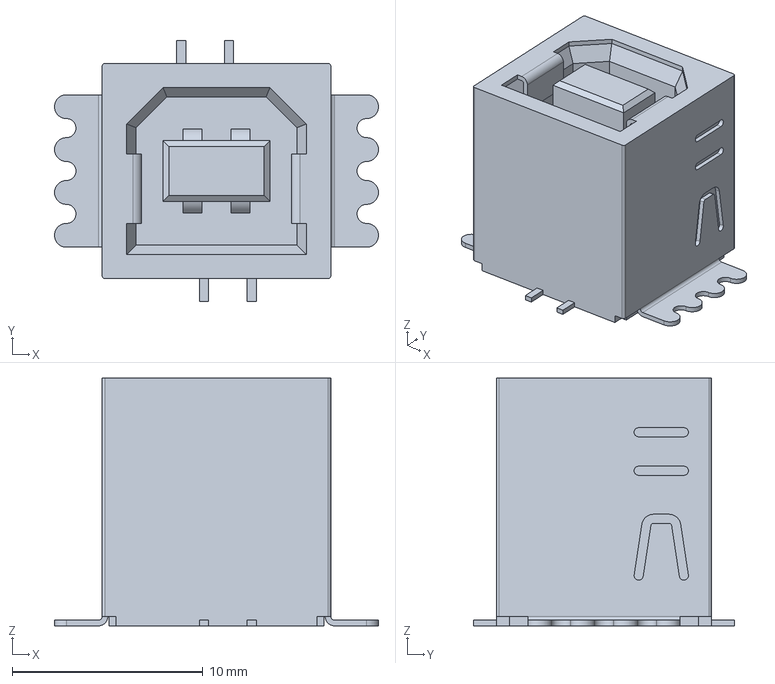
[picture p70: CAD file, 2021-02-01]
3DModels/c-1734517-1-b-3d.stp
17.0 x 13.7 x 13.0 mm
