QUT-Motorsport/QUTMS_Radio/3DModels/SOT-223.step

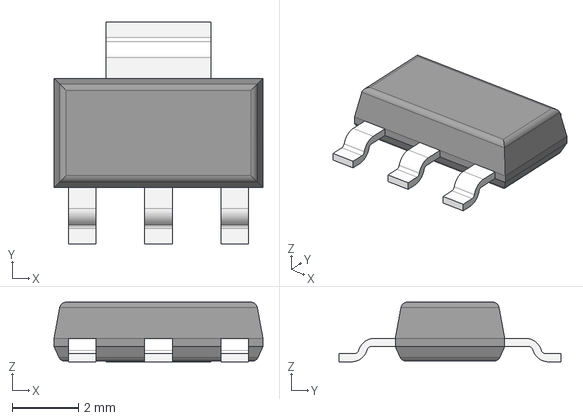
[picture p71: CAD file, 2021-02-01]
3DModels/SOT-223.step
6.30 x 6.70 x 1.80 mm
