QUT-Motorsport/QUTMS_Radio/3DModels/keystone-PN24883.STEP

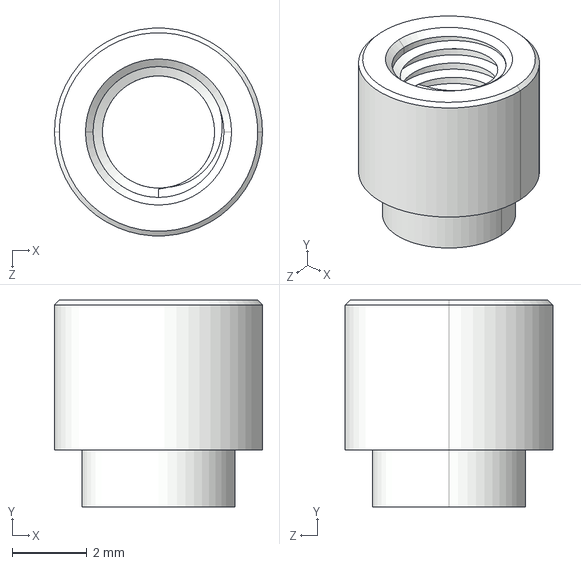
[picture p72: CAD file, 2021-01-29]
3DModels/keystone-PN24883.STEP
5.56 x 5.52 x 5.55 mm
