QUT-Motorsport/QUTMS_Radio/3DModels/CUI_PJ-102A.STEP

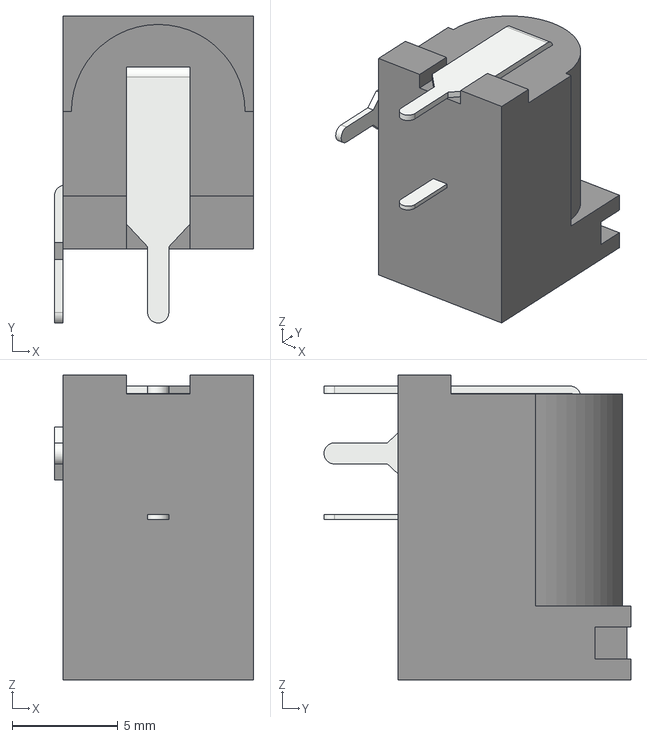
[picture p73: CAD file, 2021-01-29]
3DModels/CUI_PJ-102A.STEP
9.40 x 14.5 x 14.4 mm
