QUT-Motorsport/QUTMS_Radio/3DModels/keystone-PN24884.STEP

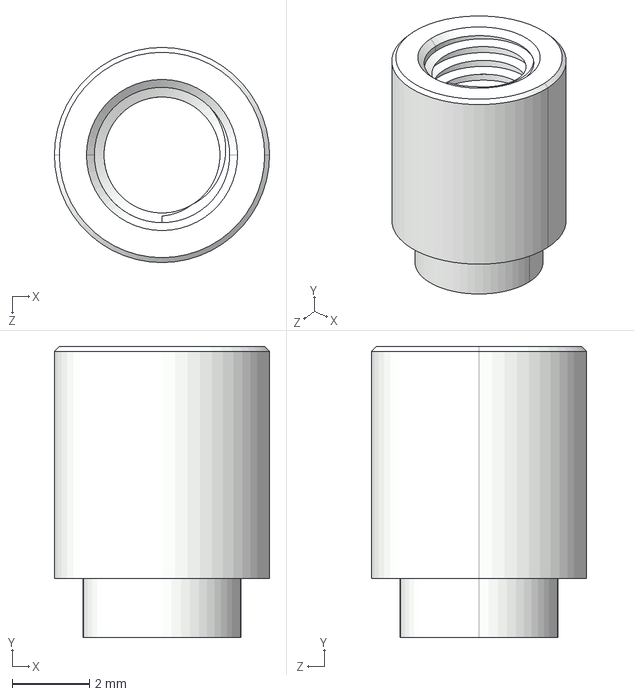
[picture p74: CAD file, 2021-01-29]
3DModels/keystone-PN24884.STEP
5.56 x 7.52 x 5.56 mm
