QUT-Motorsport/QUTMS_Radio/3DModels/TSOT-5.step

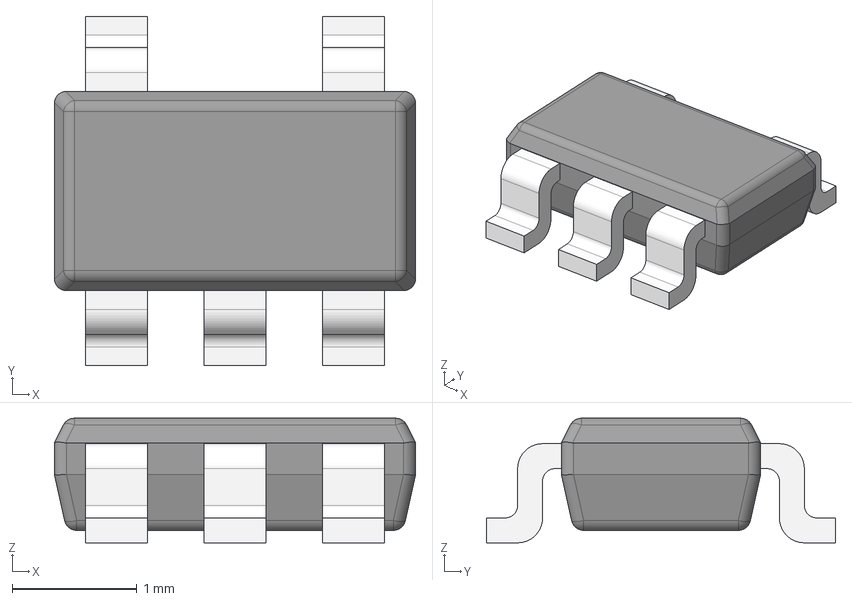
[picture p76: CAD file, 2021-01-29]
3DModels/TSOT-5.step
2.90 x 2.80 x 1.00 mm
