QUT-Motorsport/QUTMS_Radio/3DModels/0ZCJ0005FF2E.step

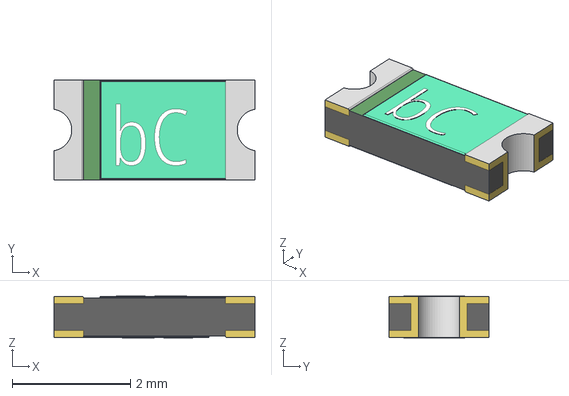
[picture p77: CAD file, 2021-01-29]
3DModels/0ZCJ0005FF2E.step
3.40 x 1.70 x 0.708 mm
