QUT-Motorsport/QUTMS_Radio/3DModels/keystone-PN24882.STEP

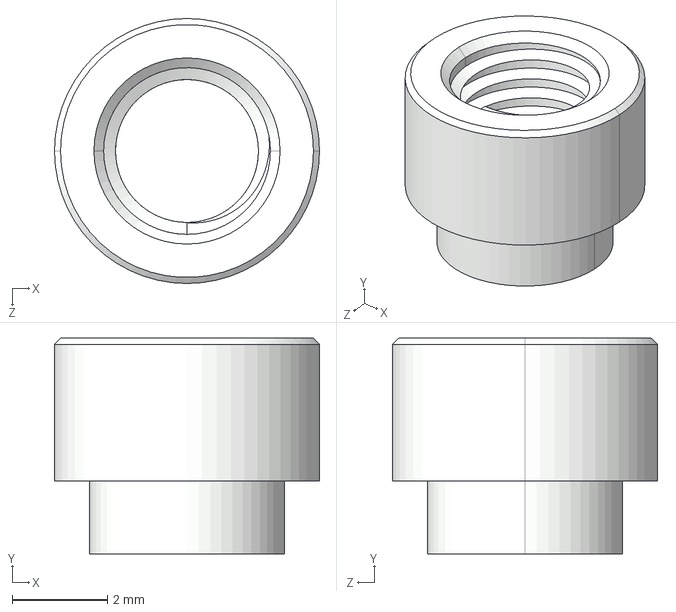
[picture p78: CAD file, 2021-01-29]
3DModels/keystone-PN24882.STEP
5.56 x 4.52 x 5.56 mm
