QUT-Motorsport/QUTMS_Radio/3DModels/c-2305018-2-a-3d.stp

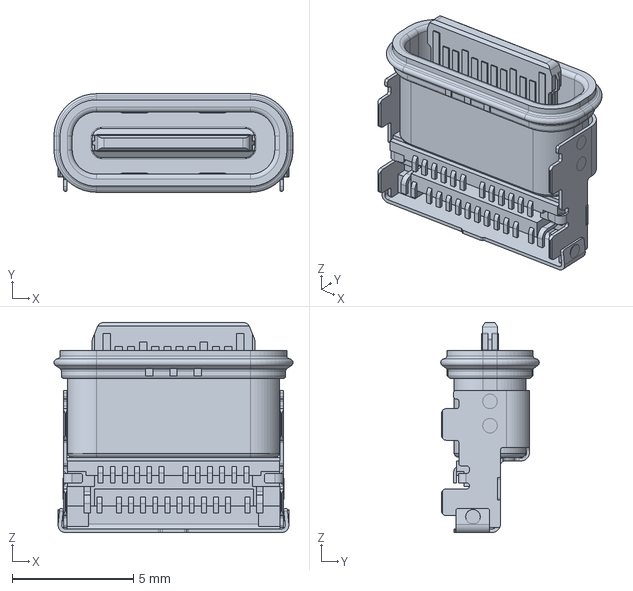
[picture p80: CAD file, 2021-01-28]
3DModels/c-2305018-2-a-3d.stp
9.84 x 4.06 x 8.65 mm
