QUT-Motorsport/QUTMS_Radio/3DModels/PCIE-036-02-F-D-RA.stp

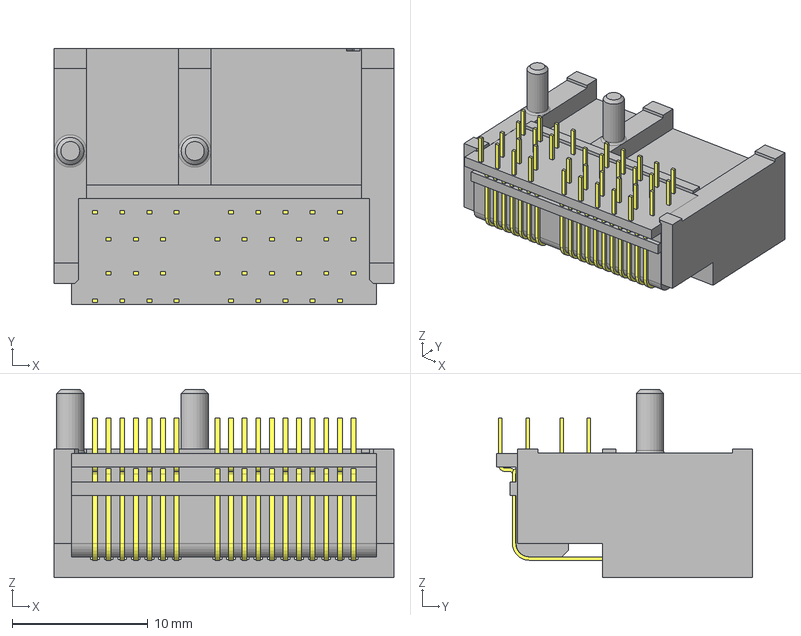
[picture p81: CAD file, 2021-01-28]
3DModels/PCIE-036-02-F-D-RA.stp
25.0 x 18.9 x 13.9 mm
_PCIE-036-02-F-D-RA_body
_PCIE-036-02-F-D-RA_pins1
_PCIE-036-02-F-D-RA_pins2
