QUT-Motorsport/QUTMS_Radio/3DModels/TDFN50P-3MMX3MM-10 v0.step

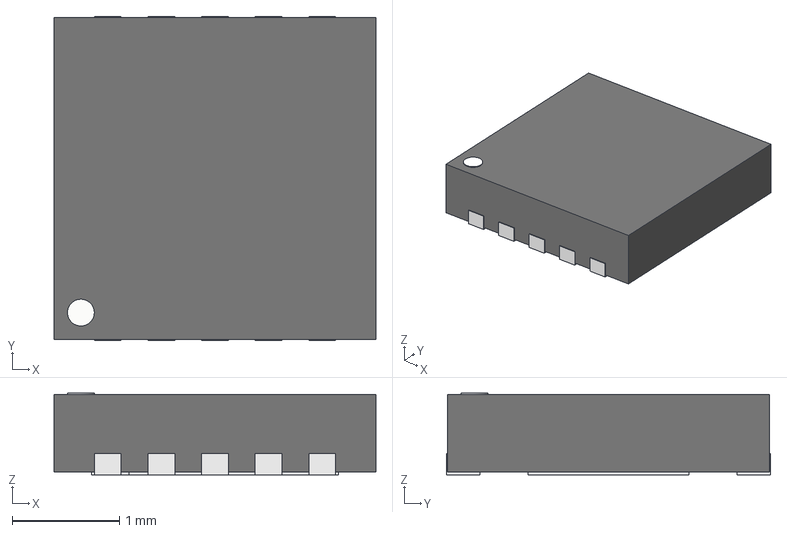
[picture p82: CAD file, 2021-01-28]
3DModels/TDFN50P-3MMX3MM-10 v0.step
3.00 x 3.02 x 0.76 mm
