QUT-Motorsport/QUTMS_Radio/3DModels/SC-74-6.stp

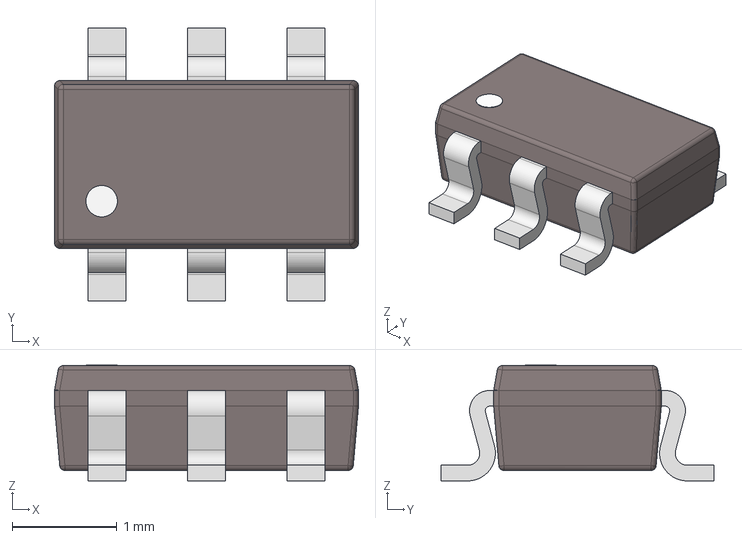
[picture p83: CAD file, 2021-01-28]
3DModels/SC-74-6.stp
2.90 x 2.60 x 1.11 mm
