QUT-Motorsport/QUTMS_Radio/3DModels/SC-74-4.stp

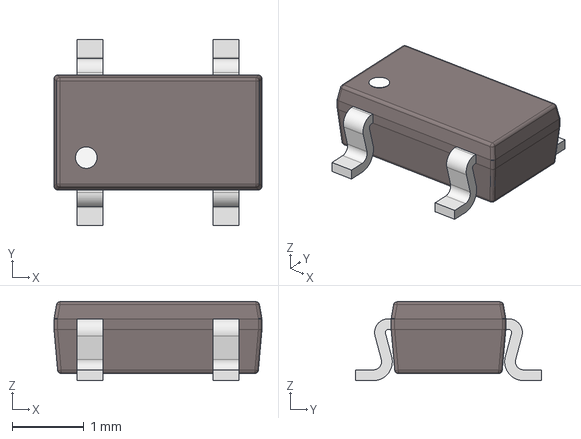
[picture p84: CAD file, 2021-01-28]
3DModels/SC-74-4.stp
2.90 x 2.60 x 1.11 mm
