QUT-Motorsport/QUTMS_Radio/3DModels/SC-74-5.stp

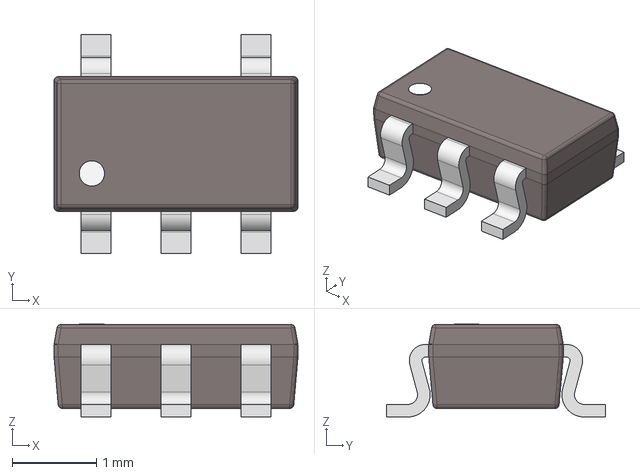
[picture p85: CAD file, 2021-01-28]
3DModels/SC-74-5.stp
2.90 x 2.60 x 1.11 mm
