QUT-Motorsport/QUTMS_Radio/3DModels/Xbee SX v3.step

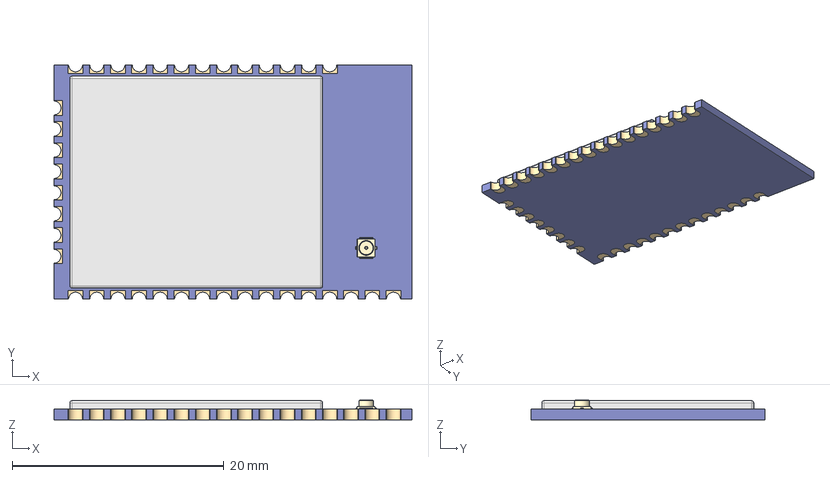
[picture p86: CAD file, 2021-01-28]
3DModels/Xbee SX v3.step
33.8 x 22.1 x 1.85 mm
