QUT-Motorsport/QUTMS_Radio/3DModels/u-blox ZED-F9P.stp

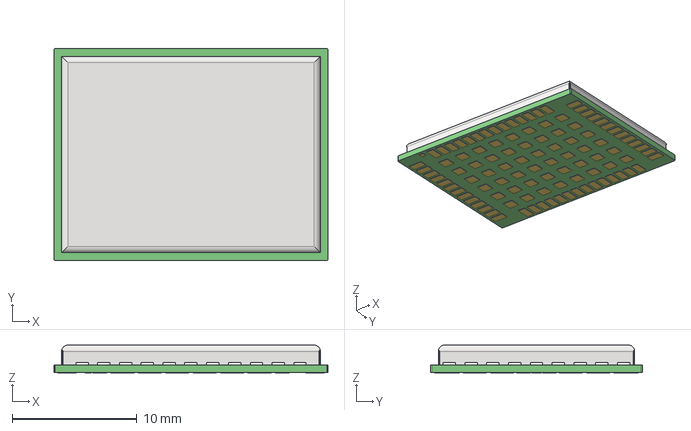
[picture p87: CAD file, 2021-01-28]
3DModels/u-blox ZED-F9P.stp
22.0 x 17.0 x 2.24 mm
