QUT-Motorsport/QUTMS_Radio/RelatedImages/coplanarWaveguideCalculation.PNG

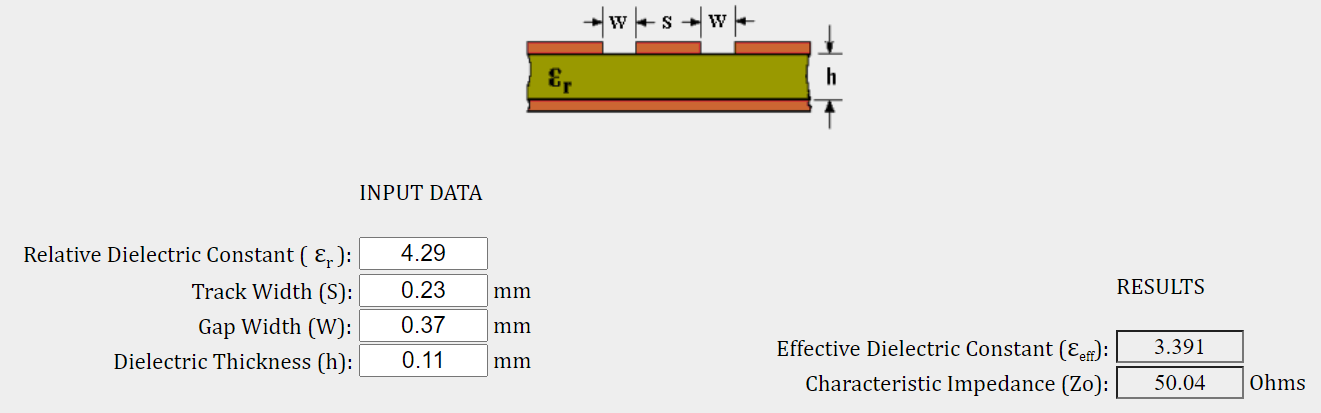
RelatedImages/coplanarWaveguideCalculation.PNG
