QUT-Motorsport/QUTMS_Radio/RelatedImages/coplanarWaveguideMaths.PNG

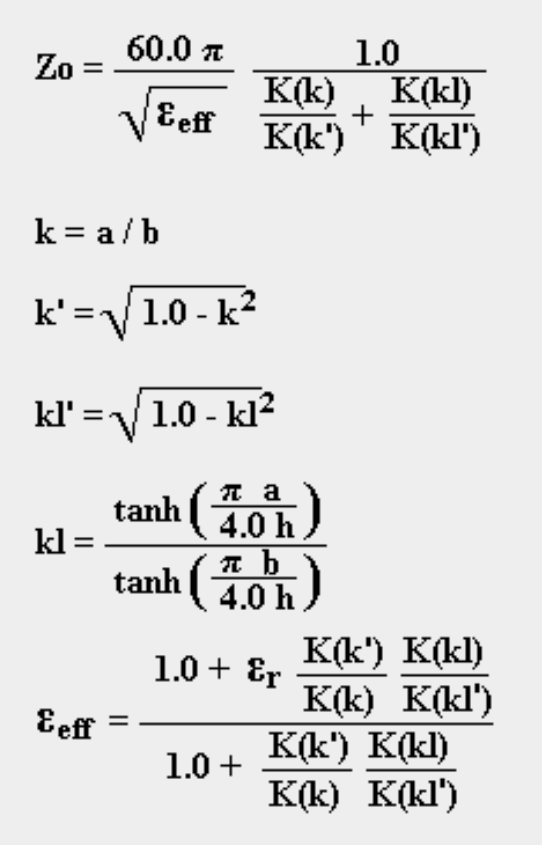
RelatedImages/coplanarWaveguideMaths.PNG
