QUT-Motorsport/QUTMS_Radio/RelatedImages/presentationAssembly_whole.PNG

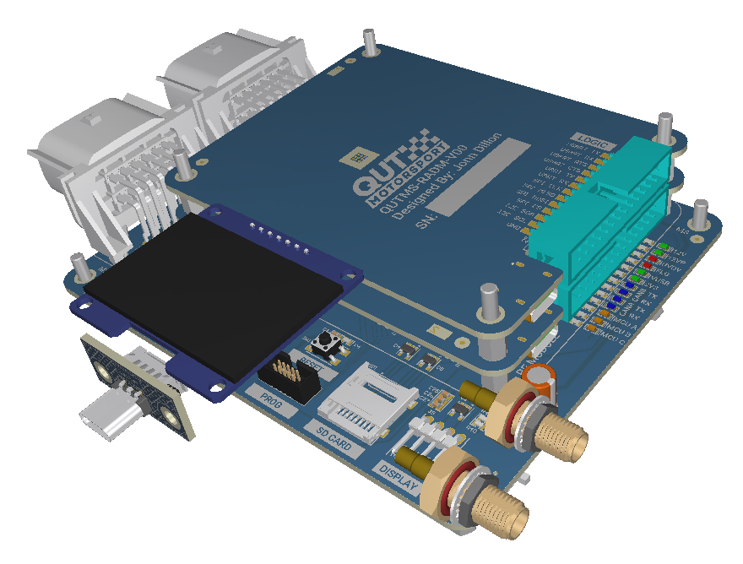
RelatedImages/presentationAssembly_whole.PNG
