QUT-Motorsport/QUTMS_Radio/ReferencesDatasheetsCalculationsLists/ZEDF9PAntennaFrontend.asc

C1: cap; 10nF
I1: current; 0.02
L1: ind; 120nH; Ipk=1.5
M1: nmos; Si1555DL_N
R1: res; 100k
R2: res; 1k
R3: res; 100k
R4: res; 10
U1: LT6001
V1: voltage; 3.3
V2: voltage; 3.2
Named nets: 0, 3V3, 3V2, DET, PWR, PWRR
.tran 0 0.01 0
