QUT-Motorsport/QUTMS_Radio/Simulations/Digi_SXRadio_RSSIPinSim.asc

C1: cap; 1µF
R1: res; 100k
V1: voltage; PULSE(0V 3.3V 0 0 0 0.007917 0.00833)
Named nets: 0, PWM, VOLT
.tran 1
